ThanicsRobotics/ProjectHaloCAD/ECAD-Files/EAGLE-Files/ThanicsHalo/Drone V3/TOF Sensor Board/TOFSensorBoard.brd

## EAGLE design ECAD-Files/EAGLE-Files/ThanicsHalo/Drone V3/TOF Sensor Board/TOFSensorBoard.brd (2018-07-10)

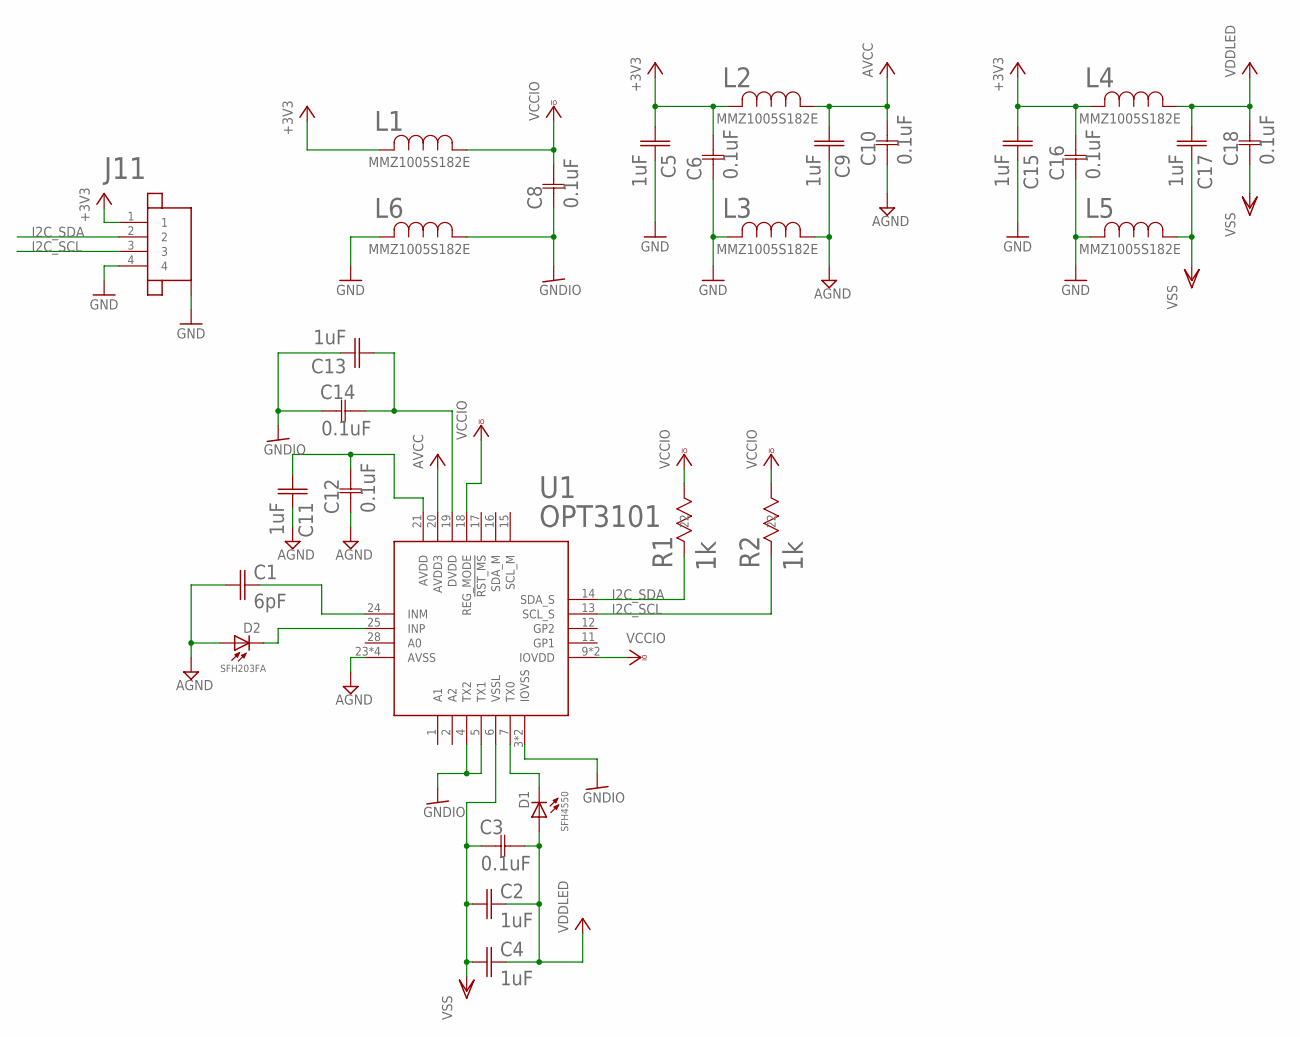
[picture p37: schematic TOFSensorBoard.sch]

Parts:
C1: 6pF; 0402_CAPACITOR
C2, C4, C5, C9, C11, C13, C15, C17: 1uF; 0603_CAPACITOR
C3, C6, C8, C10, C12, C14, C16, C18: 0.1uF; 0402-M
D1: SFH4550; 5MM_LED
D2: SFH203FA; 5MM_LED
J11: JST_SH_4POS
L1, L2, L3, L4, L5, L6: MMZ1005S182ET000IND_1005-M; IND_1005-M
R1, R2: 1k; RC0603N-M
U1: OPT3101; 28-VQFN

Connections:
+3V1: C13.1, C14.2, U1.19 (DVDD)
+3V3: C5.1, C6.2, C15.1, C16.2, J11.1, L1.2, L2.2, L4.2
AGND: C1.1, C9.2, C10.1, C11.2, C12.1, D2.A, L3.1, U1.23 (AVSS), U1.26 (AVSS), U1.27 (AVSS), U1.29 (AVSS)
AVCC: C9.1, C10.2, L2.1, U1.20 (AVDD3)
GND: C5.2, C6.1, C15.2, C16.1, J11.4, J11.P$5 (5), J11.P$6 (5), L3.2, L5.2, L6.2
GNDIO: C8.1, C13.2, C14.1, L6.1, U1.3 (IOVSS), U1.4 (TX2), U1.5 (TX1), U1.8 (IOVSS)
I2C_SCL: J11.3, R2.2 (22), U1.13 (SCL_S)
I2C_SDA: J11.2, R1.2 (22), U1.14 (SDA_S)
unnamed: C11.1, C12.2, U1.21 (AVDD)
unnamed: D1.C, U1.7 (TX0)
unnamed: C1.2, U1.24 (INM)
unnamed: D2.C, U1.25 (INP)
VCCIO: C8.2, L1.1, R1.1 (11), R2.1 (11), U1.9 (IOVDD), U1.10 (IOVDD), U1.18 (REG_MODE)
VDDLED: C2.2, C3.2, C4.2, C17.1, C18.2, D1.A, L4.1
VSS: C2.1, C3.1, C4.1, C17.2, C18.1, L5.1, U1.6 (VSSL)

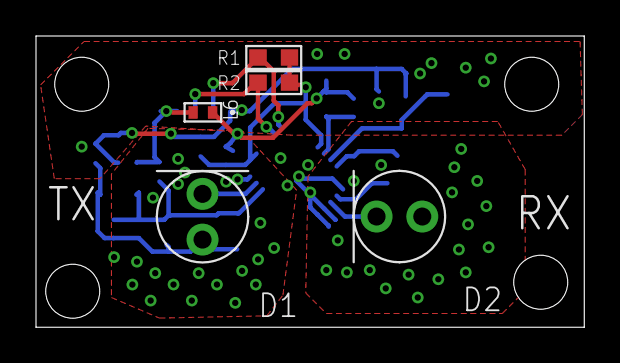
[picture p38: board TOFSensorBoard.brd from above]

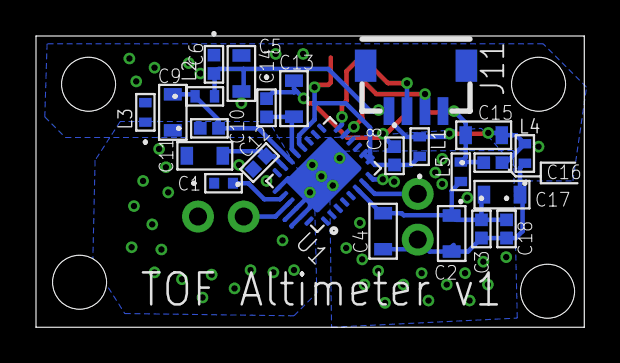
[picture p39: board TOFSensorBoard.brd from below]

Board: 4 copper layers, 30.5 x 16.2 mm, 29 parts (24 on the bottom side), 15 nets.
