ThanicsRobotics/ProjectHaloCAD/ECAD-Files/EAGLE-Files/ThanicsHalo/Drone V1/Gimbal Controller Board/Gimbal Controller Board.brd

## EAGLE design ECAD-Files/EAGLE-Files/ThanicsHalo/Drone V1/Gimbal Controller Board/Gimbal Controller Board.brd (2018-02-16, an earlier design)

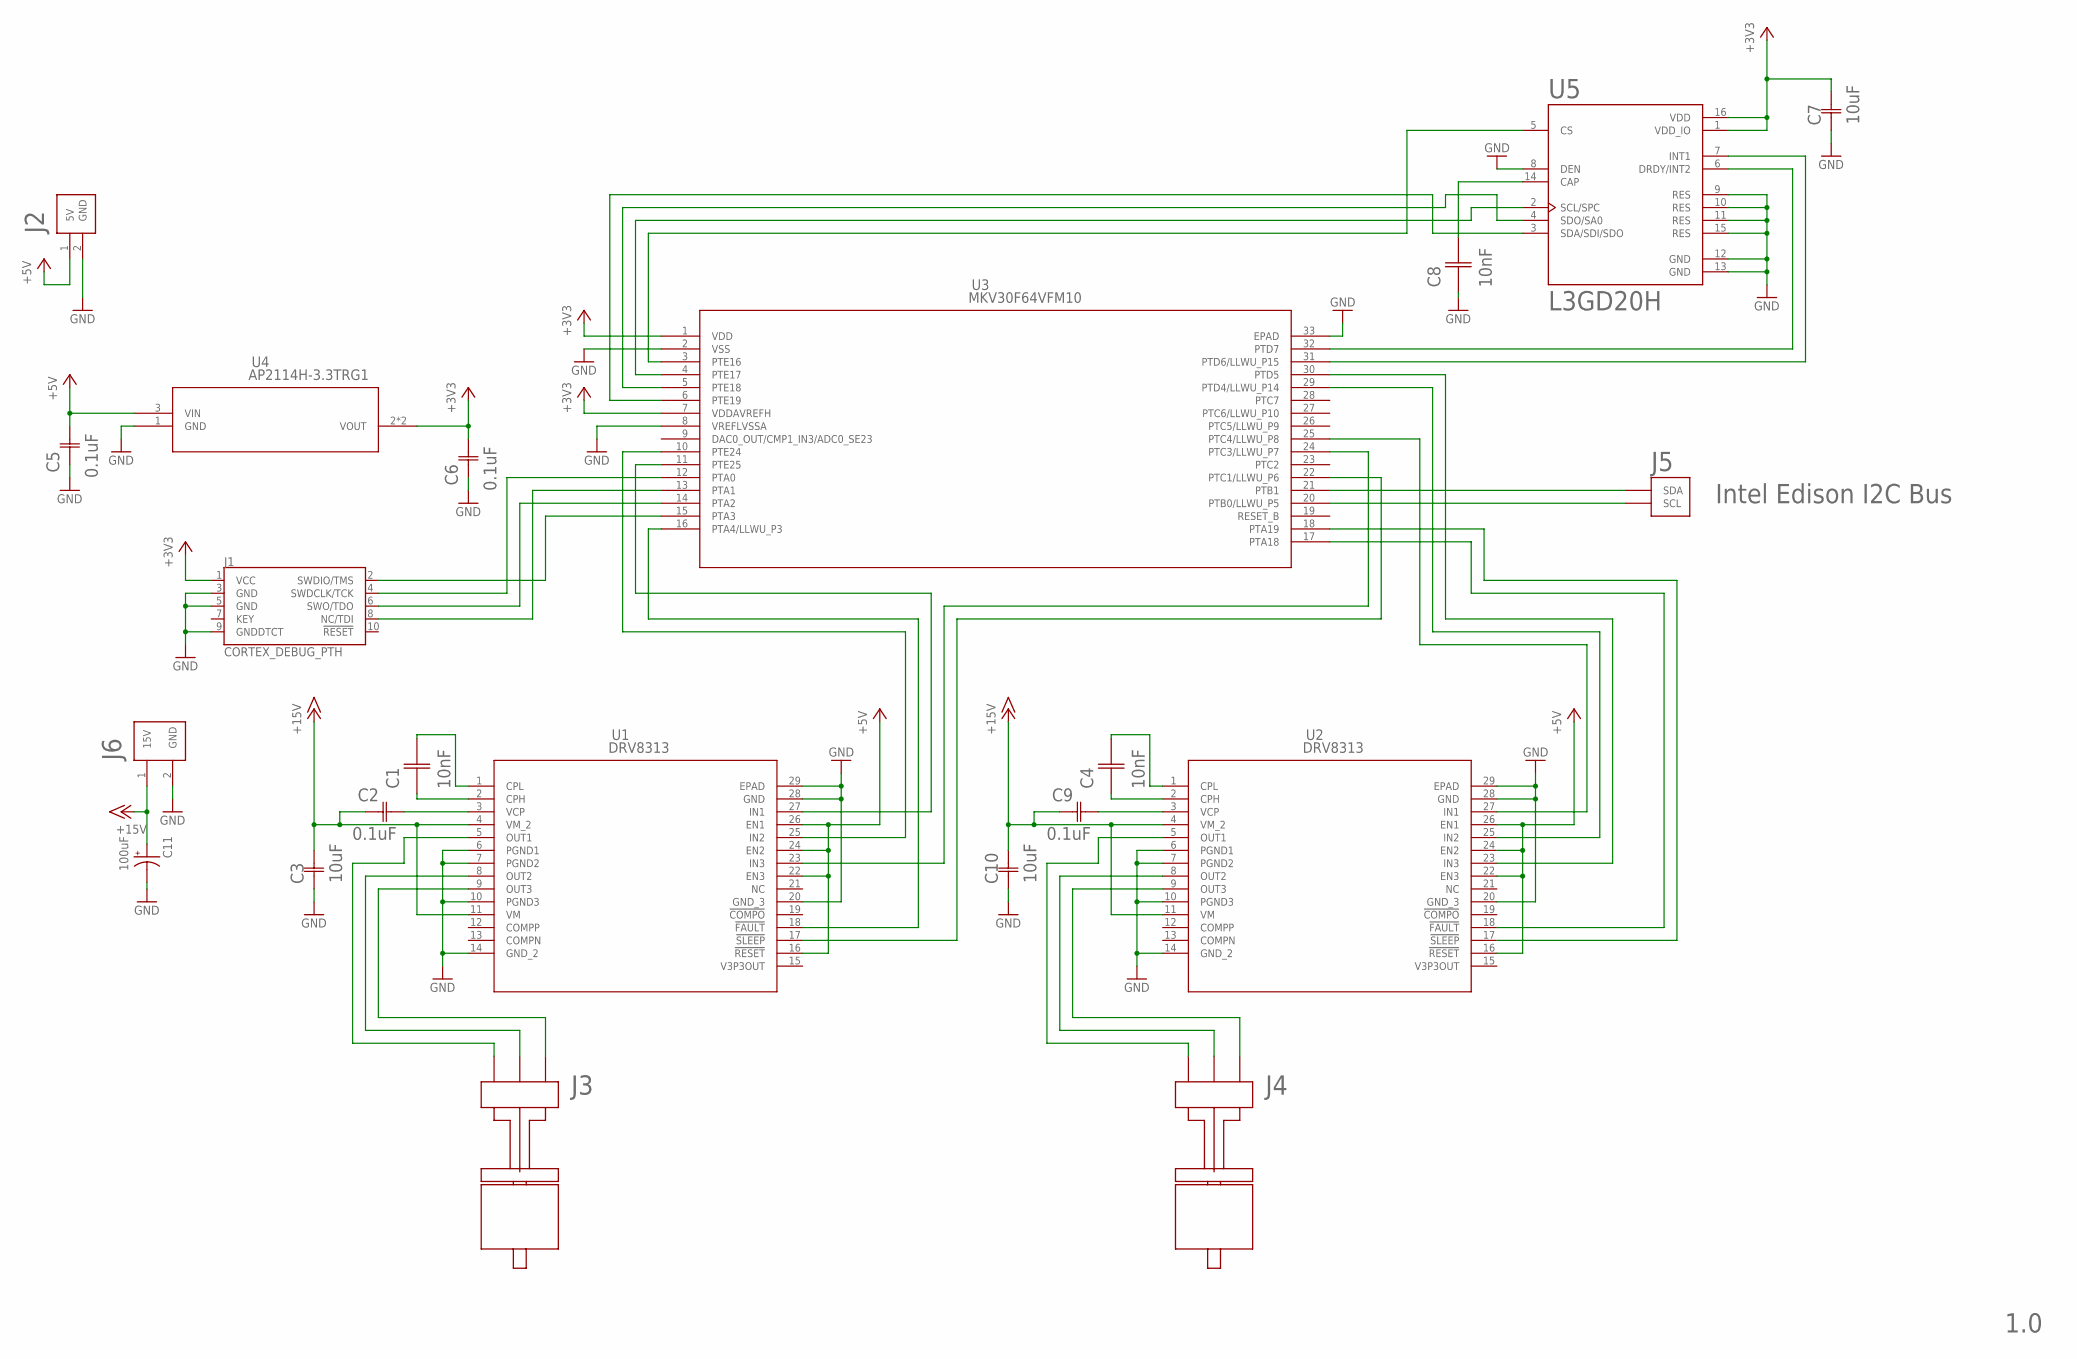
[picture p40: schematic Gimbal Controller Board.sch]

Parts:
C1, C4, C8: 10nF; 0603_CAPACITOR
C2, C5, C6, C9: 0.1uF; 0805
C3, C7, C10: 10uF; G-21
C11: 100uF; 0810_POLCAP
J1: CORTEX_DEBUG_PTH; 2X5-PTH-1.27MM
J2: POWER_CONNECTOR; XH_CONNECTOR
J3, J4: BLDC_MOTOR_CONNECTOR; JST-XH_3POS
J5: I2C_CONNECTOR; XH_CONNECTOR
J6: GIMBAL_POWER_CONNECTOR; XH_CONNECTOR
U1, U2: DRV8313; PWP28_5P18X3P1-M
U3: MKV30F64VFM10; QFN-32_5X5X0.9
U4: AP2114H-3.3TRG1; SOT-223
U5: L3GD20H; LGA16R50P7X5_300X300X100

Connections:
+3V3: C6.2, C7.2 (22), J1.1 (VCC), U3.1 (VDD), U3.7 (VDDAVREFH), U4.2 (VOUT), U4.4 (VOUT), U5.1 (VDD_IO), U5.16 (VDD)
+5V: C5.2, J2.1 (5V), U1.16 (!RESET), U1.22 (EN3), U1.24 (EN2), U1.26 (EN1), U2.16 (!RESET), U2.22 (EN3), U2.24 (EN2), U2.26 (EN1), U4.3 (VIN)
+15V: C2.1, C3.2 (22), C9.1, C10.2 (22), C11.+, J6.1 (15V), U1.4 (VM_2), U1.11 (VM), U2.4 (VM_2), U2.11 (VM)
GND: C3.1 (11), C5.1, C6.1, C7.1 (11), C8.1, C10.1 (11), C11.-, J1.3 (GND), J1.5 (GND), J1.9 (GNDDTCT), J2.2 (GND), J6.2 (GND), U1.6 (PGND1), U1.7 (PGND2), U1.10 (PGND3), U1.14 (GND_2), U1.20 (GND_3), U1.28 (GND), U1.29 (EPAD), U2.6 (PGND1), U2.7 (PGND2), U2.10 (PGND3), U2.14 (GND_2), U2.20 (GND_3), U2.28 (GND), U2.29 (EPAD), U3.2 (VSS), U3.8 (VREFLVSSA), U3.33 (EPAD), U4.1 (GND), U5.8 (DEN), U5.9 (RES), U5.10 (RES), U5.11 (RES), U5.12 (GND), U5.13 (GND), U5.15 (RES)
unnamed: C1.1, U1.2 (CPH)
unnamed: C1.2, U1.1 (CPL)
unnamed: U1.25 (IN2), U3.10 (PTE24)
unnamed: U1.17 (!SLEEP), U3.22 (PTC1/LLWU_P6)
unnamed: J3.P$1 (1), U1.5 (OUT1)
unnamed: U1.23 (IN3), U3.24 (PTC3/LLWU_P7)
unnamed: U1.18 (!FAULT), U3.16 (PTA4/LLWU_P3)
unnamed: U1.27 (IN1), U3.11 (PTE25)
unnamed: J1.4 (SWDCLK/TCK), U3.12 (PTA0)
unnamed: J1.6 (SWO/TDO), U3.14 (PTA2)
unnamed: J1.8 (NC/TDI), U3.13 (PTA1)
unnamed: J1.2 (SWDIO/TMS), U3.15 (PTA3)
unnamed: J3.P$2 (2), U1.8 (OUT2)
unnamed: J3.P$3 (3), U1.9 (OUT3)
unnamed: J5.1 (SCL), U3.20 (PTB0/LLWU_P5)
unnamed: J5.2 (SDA), U3.21 (PTB1)
unnamed: U3.3 (PTE16), U5.5 (CS)
unnamed: U3.4 (PTE17), U5.2 (SCL/SPC)
unnamed: U3.5 (PTE18), U5.4 (SDO/SA0)
unnamed: U3.6 (PTE19), U5.3 (SDA/SDI/SDO)
unnamed: C8.2, U5.14 (CAP)
unnamed: C2.2, U1.3 (VCP)
unnamed: C4.1, U2.2 (CPH)
unnamed: C4.2, U2.1 (CPL)
unnamed: U3.32 (PTD7), U5.6 (DRDY/INT2)
unnamed: U3.31 (PTD6/LLWU_P15), U5.7 (INT1)
unnamed: U2.25 (IN2), U3.29 (PTD4/LLWU_P14)
unnamed: U2.27 (IN1), U3.25 (PTC4/LLWU_P8)
unnamed: U2.23 (IN3), U3.30 (PTD5)
unnamed: U2.18 (!FAULT), U3.17 (PTA18)
unnamed: U2.17 (!SLEEP), U3.18 (PTA19)
unnamed: J4.P$1 (1), U2.5 (OUT1)
unnamed: J4.P$2 (2), U2.8 (OUT2)
unnamed: J4.P$3 (3), U2.9 (OUT3)
unnamed: C9.2, U2.3 (VCP)

Notes on the sheet:
Intel Edison I2C Bus
1.0

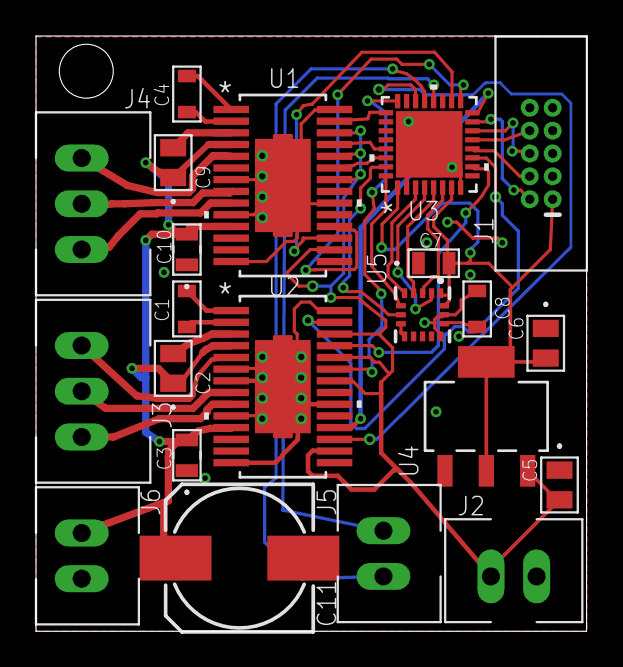
[picture p41: board ECAD-Files/EAGLE-Files/ThanicsHalo/Drone V1/Gimbal Controller Board/G… from above]

Board: 2 copper layers, 30.6 x 33.1 mm, 22 parts (0 on the bottom side), 39 nets.
