ThanicsRobotics/ProjectHaloCAD/ECAD-Files/EAGLE-Files/ThanicsHalo/Drone V2/Sensor Board B/Sensor Board B.brd

## EAGLE design ECAD-Files/EAGLE-Files/ThanicsHalo/Drone V2/Sensor Board B/Sensor Board B.brd (2018-02-16, an earlier design)

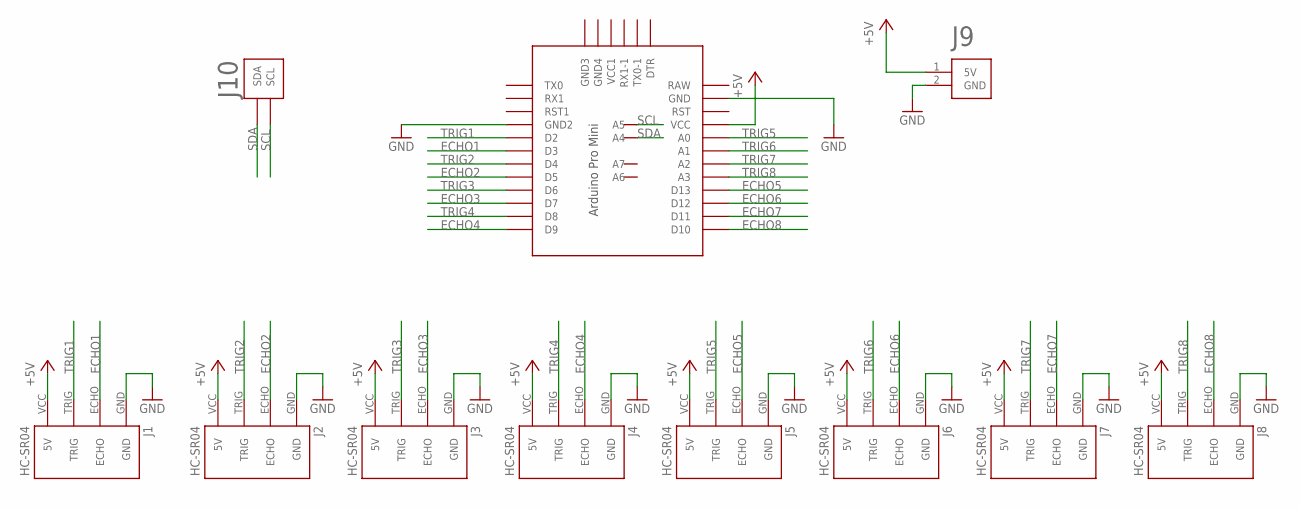
[picture p42: schematic Sensor Board B.sch]

Parts:
J1, J2, J3, J4, J5, J6, J7, J8: HC-SR04; HC-SR04_FOOTPRINT
J9: POWER_CONNECTOR; XH_CONNECTOR
J10: I2C_CONNECTOR; XH_CONNECTOR
U1: PRO-MINI-2

Connections:
+5V: J1.VCC (5V), J2.VCC (5V), J3.VCC (5V), J4.VCC (5V), J5.VCC (5V), J6.VCC (5V), J7.VCC (5V), J8.VCC (5V), J9.1 (5V), U1.VCC
ECHO1: J1.ECHO, U1.D3
ECHO2: J2.ECHO, U1.D5
ECHO3: J3.ECHO, U1.D7
ECHO4: J4.ECHO, U1.D9
ECHO5: J5.ECHO, U1.D13
ECHO6: J6.ECHO, U1.D12
ECHO7: J7.ECHO, U1.D11
ECHO8: J8.ECHO, U1.D10
GND: J1.GND, J2.GND, J3.GND, J4.GND, J5.GND, J6.GND, J7.GND, J8.GND, J9.2 (GND), U1.GND, U1.GND1 (GND2)
SCL: J10.1 (SCL), U1.A5
SDA: J10.2 (SDA), U1.A4
TRIG1: J1.TRIG, U1.D2
TRIG2: J2.TRIG, U1.D4
TRIG3: J3.TRIG, U1.D6
TRIG4: J4.TRIG, U1.D8
TRIG5: J5.TRIG, U1.A0
TRIG6: J6.TRIG, U1.A1
TRIG7: J7.TRIG, U1.A2
TRIG8: J8.TRIG, U1.A3

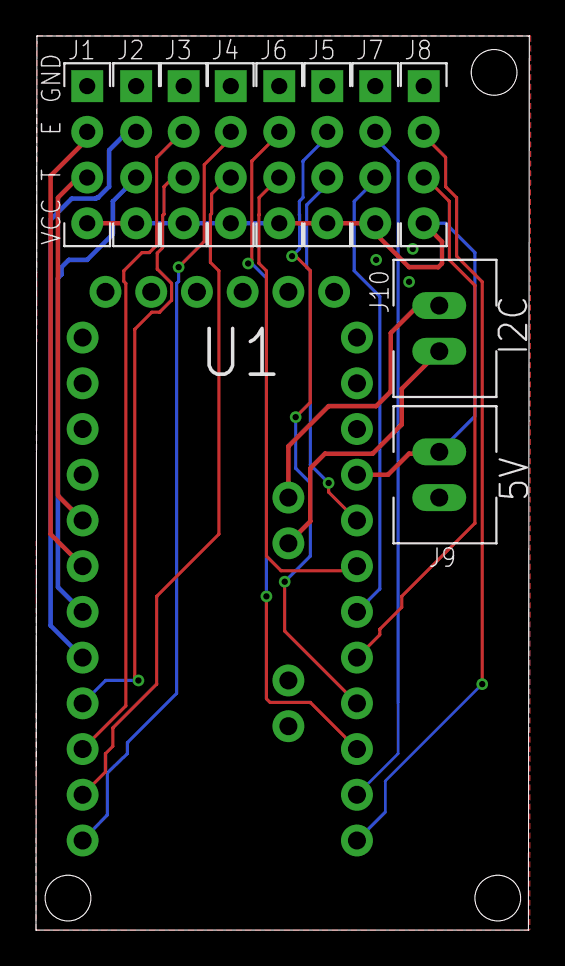
[picture p43: board Sensor Board B.brd from above]

Board: 2 copper layers, 27.4 x 49.7 mm, 11 parts (0 on the bottom side), 20 nets.
