ThanicsRobotics/ProjectHaloCAD/ECAD-Files/EAGLE-Files/ThanicsHalo/Drone V2/Drone-Battery Connection/Drone-Battery Connection.brd

## EAGLE design ECAD-Files/EAGLE-Files/ThanicsHalo/Drone V2/Drone-Battery Connection/Drone-Battery Connection.brd (2018-02-16, an earlier design)

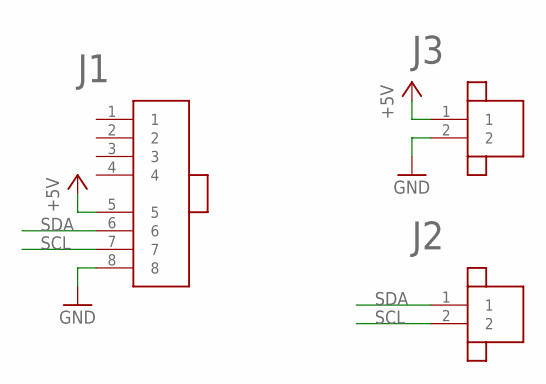
[picture p44: schematic Drone-Battery Connection.sch]

Parts:
J1: SPRING_BTB_8POS_MALE
J2, J3: JST_SH_2POS

Connections:
+5V: J1.5, J3.1
GND: J1.8, J3.2
SCL: J1.7, J2.2
SDA: J1.6, J2.1

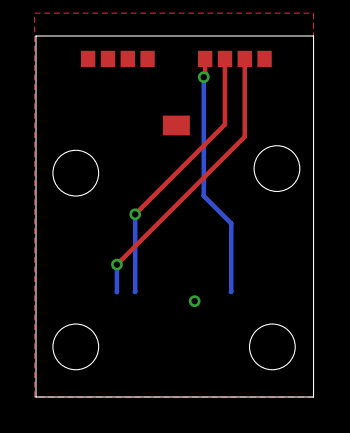
[picture p45: board Drone-Battery Connection.brd from above]

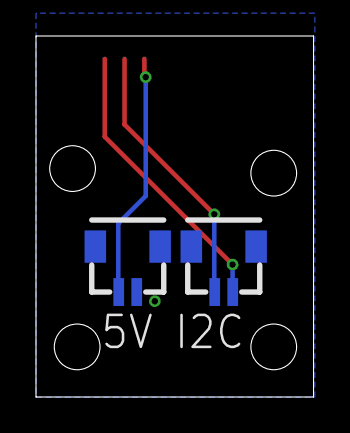
[picture p46: board Drone-Battery Connection.brd from below]

Board: 2 copper layers, 15.4 x 20.1 mm, 3 parts (2 on the bottom side), 4 nets.
