ThanicsRobotics/ProjectHaloCAD/ECAD-Files/EAGLE-Files/ThanicsHalo/Drone V1/Relay Board A/Relay Board A.brd

## EAGLE design ECAD-Files/EAGLE-Files/ThanicsHalo/Drone V1/Relay Board A/Relay Board A.brd (2018-02-16, an earlier design)

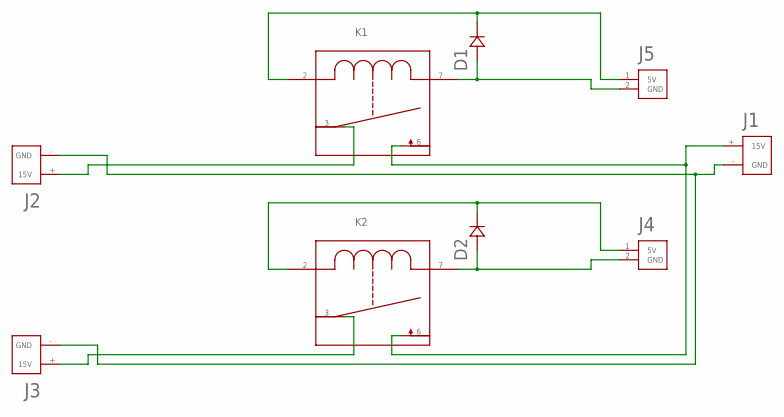
[picture p47: schematic Relay Board A.sch]

Parts:
D1, D2: 1N4148W-7-FSOD123-M; SOD123-M
J1, J2, J3: ESC_CONTACTS; XT60_CONNECTOR
J4, J5: POWER_CONNECTOR; XH_CONNECTOR
K1, K2: T9AS1D12-24; RELAY_T9AS

Connections:
GND: J1.- (GND), J2.- (GND), J3.- (GND)
unnamed: J1.+ (15V), K1.6 (3), K2.6 (3)
unnamed: J2.+ (15V), K1.3 (2)
unnamed: J3.+ (15V), K2.3 (2)
unnamed: D1.C (12), J5.1 (5V), K1.2 (1)
unnamed: D1.A (21), J5.2 (GND), K1.7 (4)
unnamed: D2.C (12), J4.1 (5V), K2.2 (1)
unnamed: D2.A (21), J4.2 (GND), K2.7 (4)

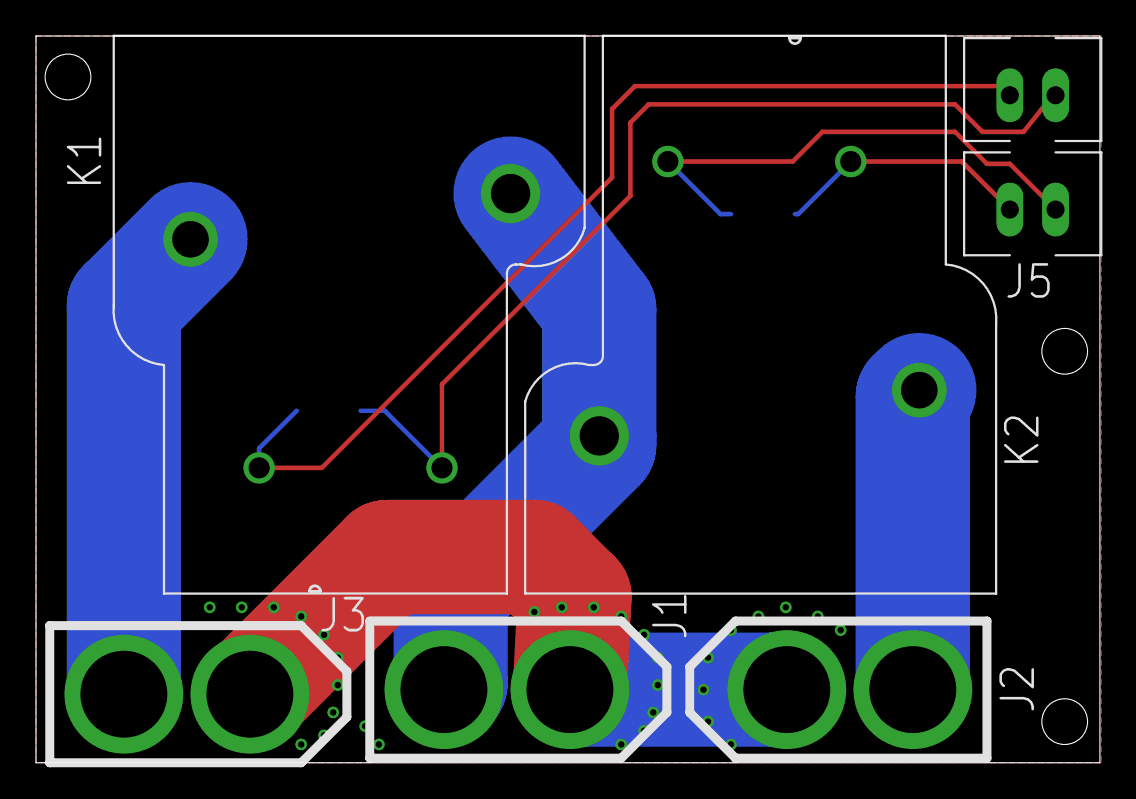
[picture p48: board Relay Board A.brd from above]

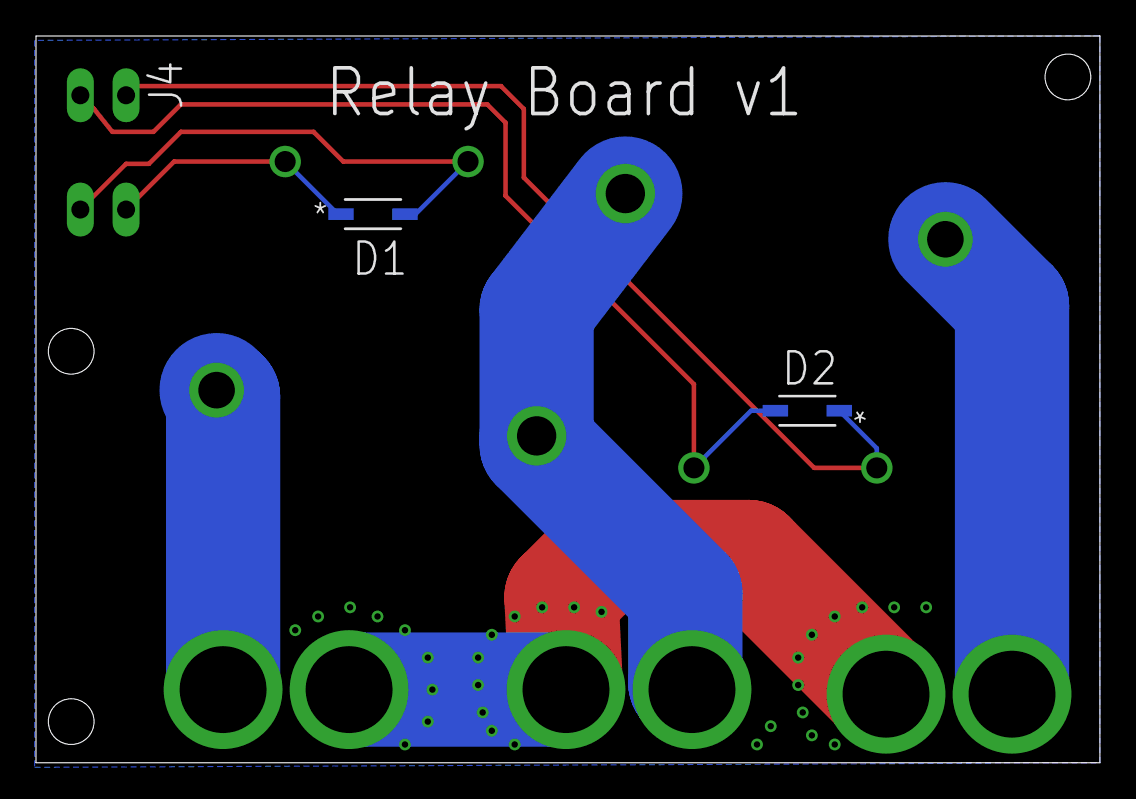
[picture p49: board Relay Board A.brd from below]

Board: 2 copper layers, 59.1 x 40.4 mm, 9 parts (2 on the bottom side), 8 nets.
