ThanicsRobotics/ProjectHaloCAD/ECAD-Files/EAGLE-Files/ThanicsHalo/Drone V1/Central Board/Central Board.brd

## EAGLE design ECAD-Files/EAGLE-Files/ThanicsHalo/Drone V1/Central Board/Central Board.brd (2018-02-16, an earlier design)

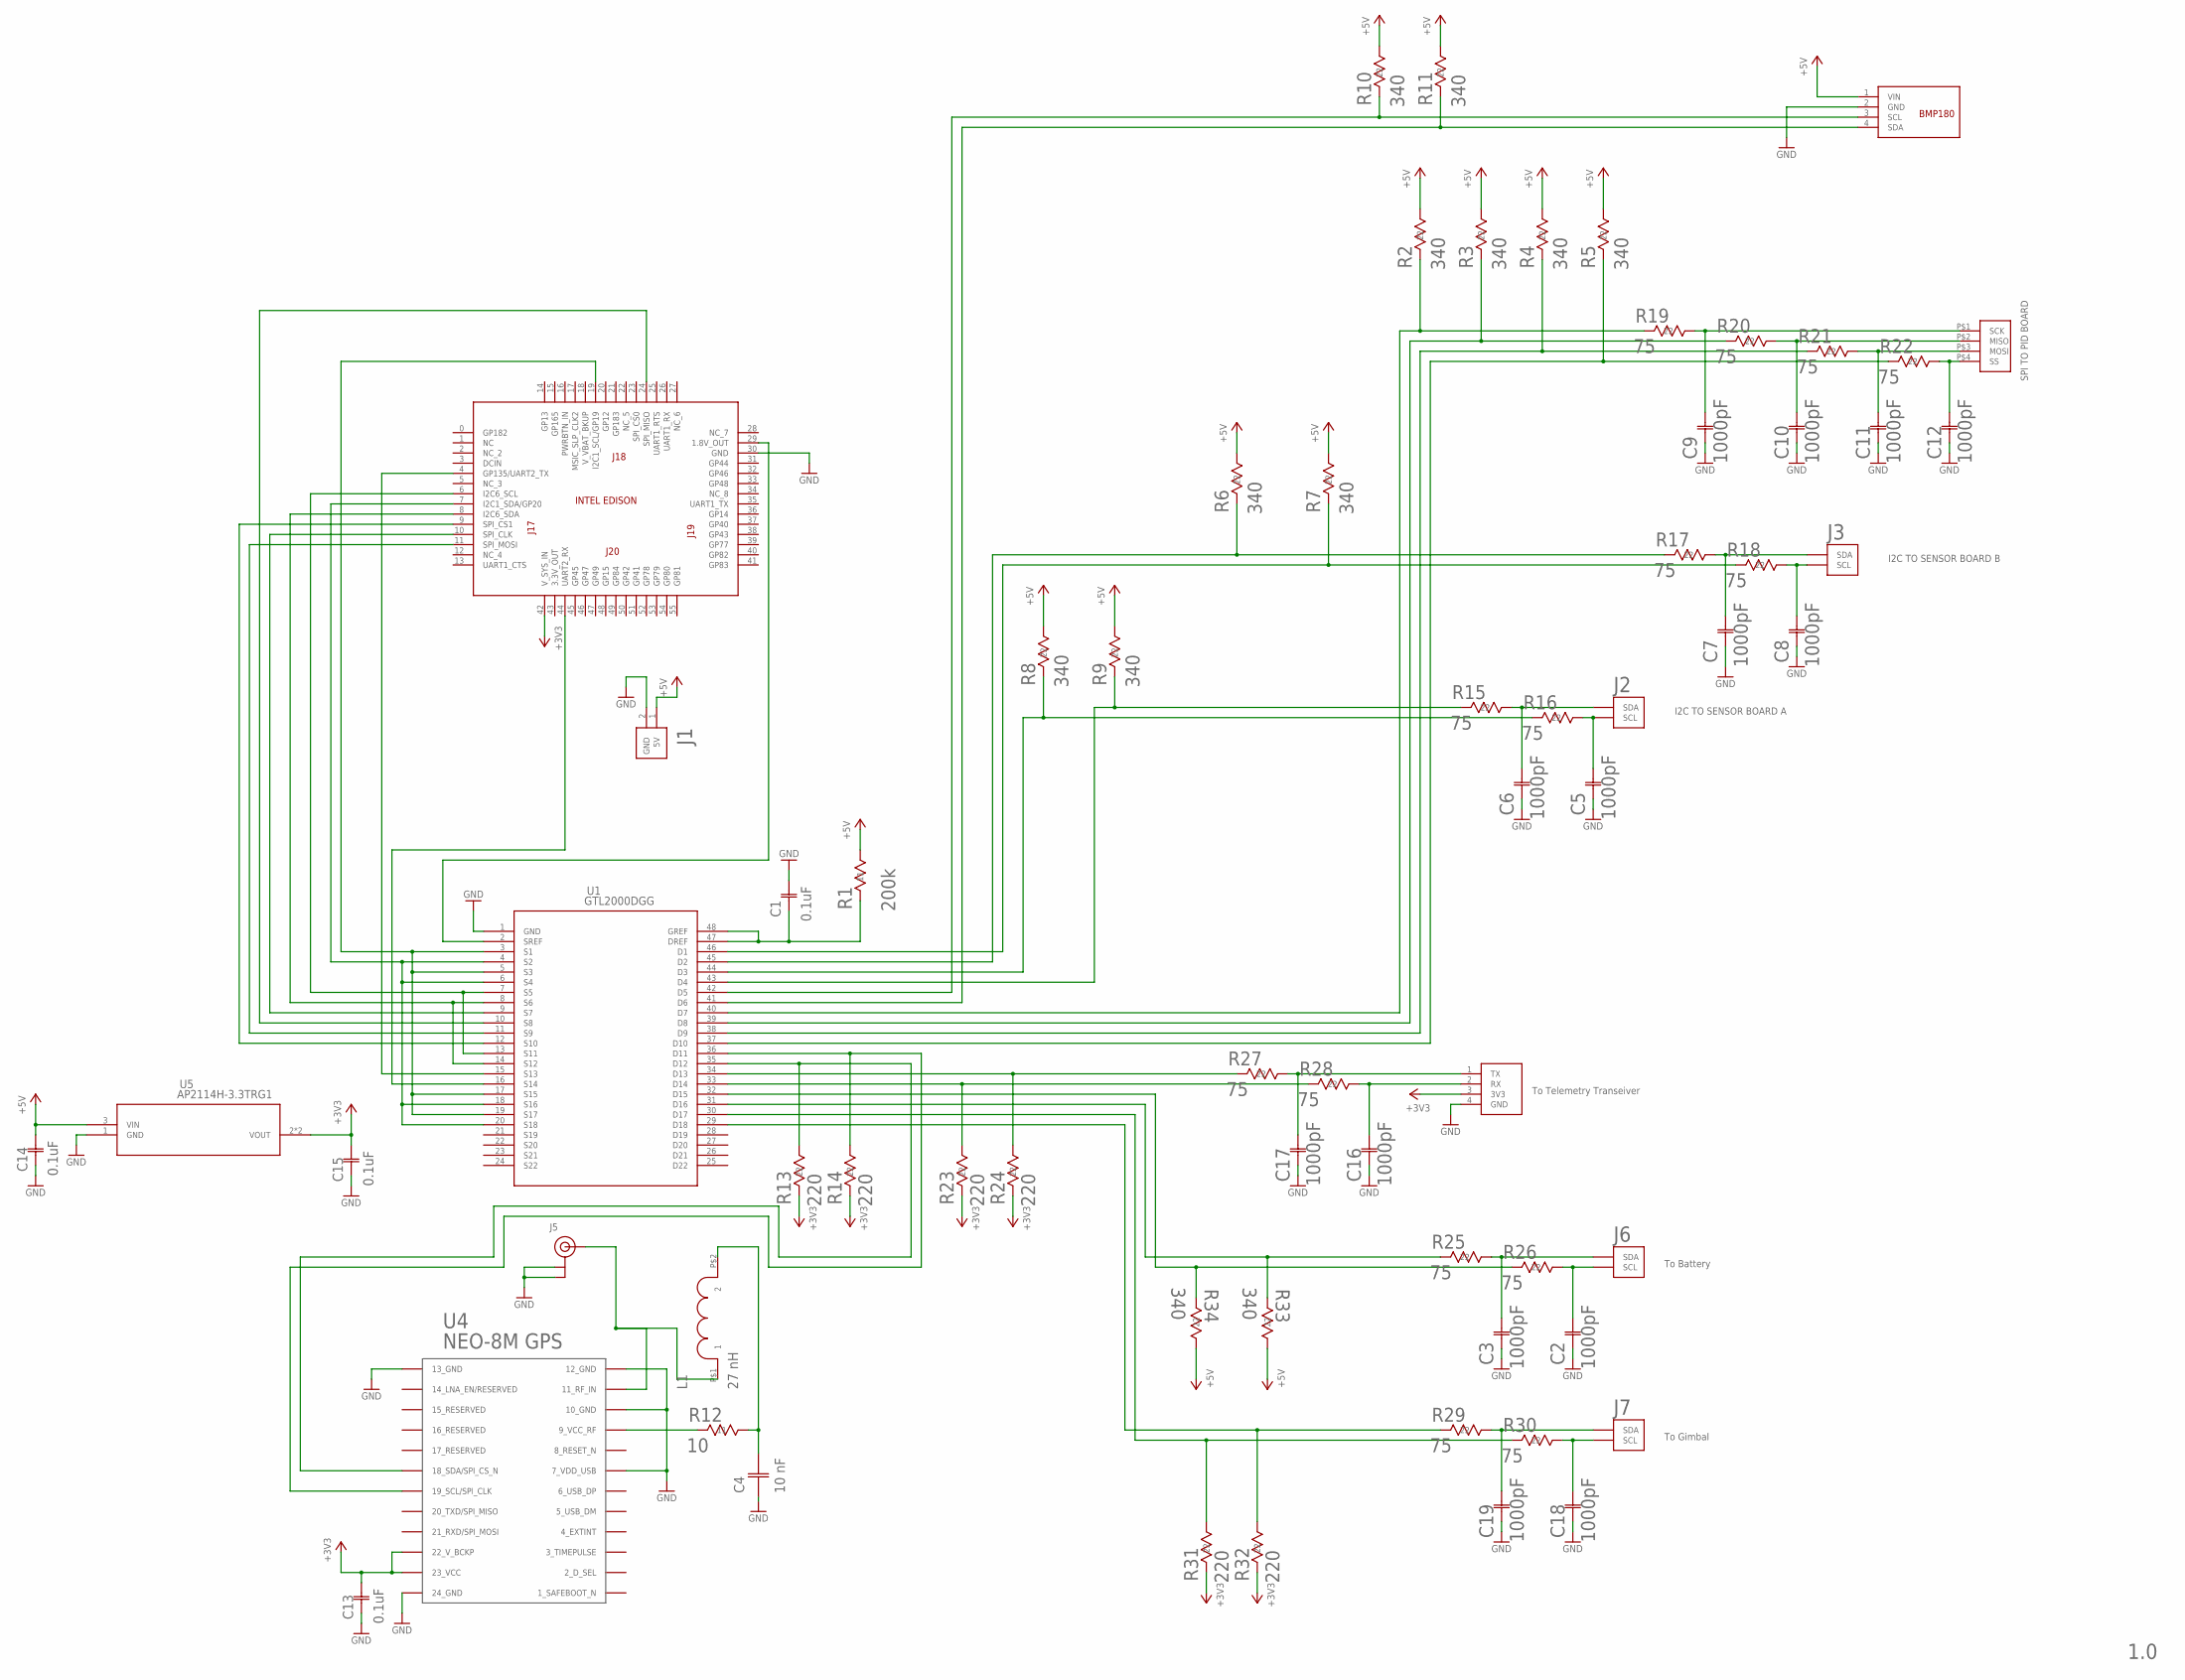
[picture p50: schematic Central Board.sch]

Parts:
C1, C13, C14, C15: 0.1uF; 0805
C2, C3, C5, C6, C7, C8, C9, C10, C11, C12, C16, C17, C18, C19: 1000pF; G-155-M
C4: 10 nF; 0603_CAPACITOR
J1: POWER_CONNECTOR; XH_CONNECTOR
J2, J3, J6, J7: I2C_CONNECTOR; XH_CONNECTOR
J4: SPI_CONNECTOR; JST-XH_4POS
J5: U.FL
L1: 27 nH; 0402_INDUCTOR
R1: 200k; STA_RMCF0603
R2, R3, R4, R5, R6, R7, R8, R9, R10, R11, R33, R34: 340; RC0603N
R12: 10; STA_RNCP0805-M
R13, R14, R23, R24, R31, R32: 220; RC0603N-M
R15, R16, R17, R18, R19, R20, R21, R22, R25, R26, R27, R28, R29, R30: 75; RC0402N-M
U1: GTL2000DGG; SOT362-1
U3: INTEL_EDISON
U4: NEO-M8
U5: AP2114H-3.3TRG1; SOT-223
U9: BMP180_BARO
U$1: 4_PIN_TELE_CONNECTOR

Connections:
3.3V_OUT: U3.43 (3.3V_OUT)
+3V3: C13.2, C15.2, R13.2 (22), R14.2 (22), R23.2 (22), R24.2 (22), R31.2 (22), R32.2 (22), U3.42 (V_SYS_IN), U4.22 (22_V_BCKP), U4.23 (23_VCC), U5.2 (VOUT), U5.4 (VOUT), U$1.3 (3V3)
+5V: C14.2, J1.1 (5V), R1.2 (22), R2.1 (11), R3.1 (11), R4.1 (11), R5.1 (11), R6.1 (11), R7.1 (11), R8.1 (11), R9.1 (11), R10.1 (11), R11.1 (11), R33.1 (11), R34.1 (11), U5.3 (VIN), U9.1 (VIN)
DCIN: U3.3 (DCIN)
GND: C1.2, C2.1 (11), C3.1 (11), C4.1, C5.1 (11), C6.1 (11), C7.1 (11), C8.1 (11), C9.1 (11), C10.1 (11), C11.1 (11), C12.1 (11), C13.1, C14.1, C15.1, C16.1 (11), C17.1 (11), C18.1 (11), C19.1 (11), J1.2 (GND), J5.P$1 (GND), J5.P$2 (GND), U1.1 (GND), U3.30 (GND), U4.7 (7_VDD_USB), U4.10 (10_GND), U4.12 (12_GND), U4.13 (13_GND), U4.24 (24_GND), U5.1 (GND), U9.2 (GND), U$1.4 (GND)
MSIC_SLP_CLK2: U3.17 (MSIC_SLP_CLK2)
unnamed: J5.P$3 (SIGNAL), L1.P$1 (1), U4.11 (11_RF_IN)
unnamed: U1.3 (S1), U1.5 (S3), U1.17 (S15), U1.19 (S17), U3.19 (I2C1_SCL/GP19)
unnamed: U1.4 (S2), U1.6 (S4), U1.18 (S16), U1.20 (S18), U3.7 (I2C1_SDA/GP20)
unnamed: R7.2 (22), R18.2 (22), U1.46 (D1)
unnamed: R6.2 (22), R17.2 (22), U1.45 (D2)
unnamed: C18.2 (22), J7.1 (SCL), R30.1 (11)
unnamed: R9.2 (22), R15.2 (22), U1.43 (D4)
unnamed: U1.7 (S5), U1.13 (S11), U3.6 (I2C6_SCL)
unnamed: U1.8 (S6), U1.14 (S12), U3.8 (I2C6_SDA)
unnamed: R10.2 (22), U1.42 (D5), U9.3 (SCL)
unnamed: U1.2 (SREF), U3.29 (1.8V_OUT)
unnamed: R14.1 (11), U1.36 (D11), U4.19 (19_SCL/SPI_CLK)
unnamed: R12.1 (11), U4.9 (9_VCC_RF)
unnamed: R11.2 (22), U1.41 (D6), U9.4 (SDA)
unnamed: U1.9 (S7), U3.10 (SPI_CLK)
unnamed: C19.2 (22), J7.2 (SDA), R29.1 (11)
unnamed: U1.10 (S8), U3.24 (SPI_MISO)
unnamed: U1.16 (S14), U3.44 (UART2_RX)
unnamed: U1.11 (S9), U3.11 (SPI_MOSI)
unnamed: U1.15 (S13), U3.4 (GP135/UART2_TX)
unnamed: U1.12 (S10), U3.9 (SPI_CS1)
unnamed: R23.1 (11), R28.2 (22), U1.33 (D14)
unnamed: C1.1, R1.1 (11), U1.47 (DREF), U1.48 (GREF)
unnamed: R24.1 (11), R27.2 (22), U1.34 (D13)
unnamed: C4.2, L1.P$2 (2), R12.2 (22)
unnamed: R13.1 (11), U1.35 (D12), U4.18 (18_SDA/SPI_CS_N)
unnamed: C5.2 (22), J2.1 (SCL), R16.1 (11)
unnamed: R8.2 (22), R16.2 (22), U1.44 (D3)
unnamed: C6.2 (22), J2.2 (SDA), R15.1 (11)
unnamed: C8.2 (22), J3.1 (SCL), R18.1 (11)
unnamed: C7.2 (22), J3.2 (SDA), R17.1 (11)
unnamed: R30.2 (22), R31.1 (11), U1.30 (D17)
unnamed: C12.2 (22), J4.P$4 (SS), R22.1 (11)
unnamed: C11.2 (22), J4.P$3 (MOSI), R21.1 (11)
unnamed: C9.2 (22), J4.P$1 (SCK), R19.1 (11)
unnamed: C10.2 (22), J4.P$2 (MISO), R20.1 (11)
unnamed: C2.2 (22), J6.1 (SCL), R26.1 (11)
unnamed: R29.2 (22), R32.1 (11), U1.29 (D18)
unnamed: C3.2 (22), J6.2 (SDA), R25.1 (11)
unnamed: C16.2 (22), R28.1 (11), U$1.2 (RX)
unnamed: R25.2 (22), R33.2 (22), U1.31 (D16)
unnamed: C17.2 (22), R27.1 (11), U$1.1 (TX)
unnamed: R26.2 (22), R34.2 (22), U1.32 (D15)
unnamed: R5.2 (22), R22.2 (22), U1.37 (D10)
unnamed: R4.2 (22), R21.2 (22), U1.38 (D9)
unnamed: R3.2 (22), R20.2 (22), U1.39 (D8)
unnamed: R2.2 (22), R19.2 (22), U1.40 (D7)
PWRBTN_IN: U3.16 (PWRBTN_IN)
V_VBAT_BKUP: U3.18 (V_VBAT_BKUP)

Notes on the sheet:
I2C TO SENSOR BOARD A
I2C TO SENSOR BOARD B
SPI TO PID BOARD
To Telemetry Transeiver
To Battery
To Gimbal
1.0

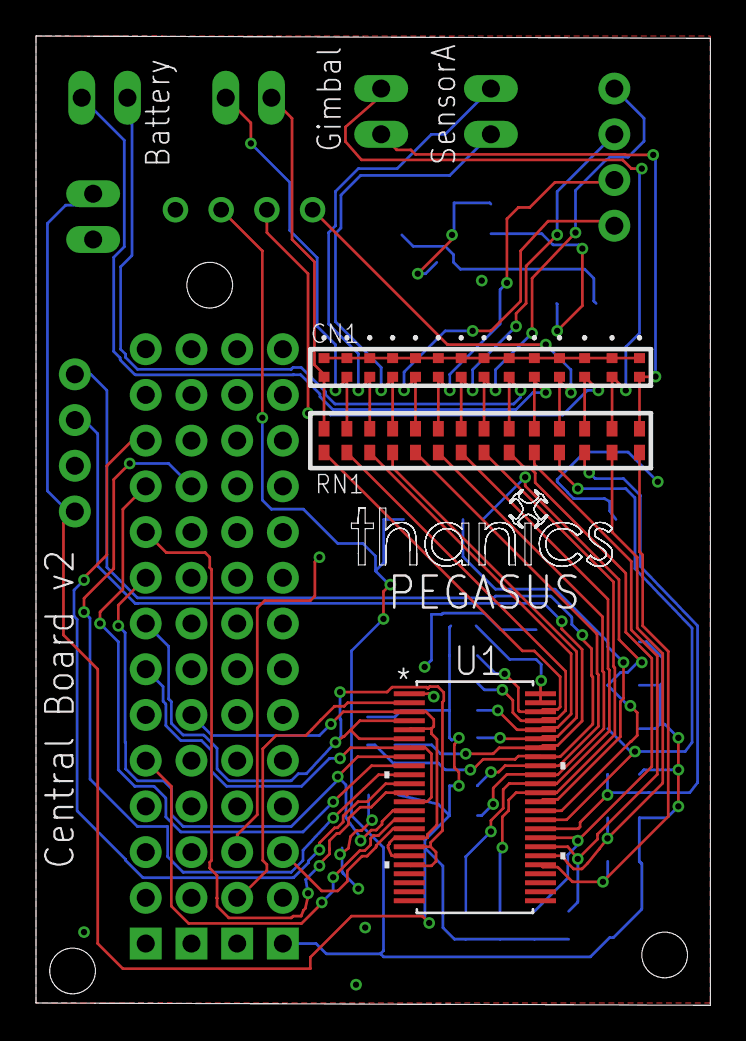
[picture p51: board Central Board.brd from above]

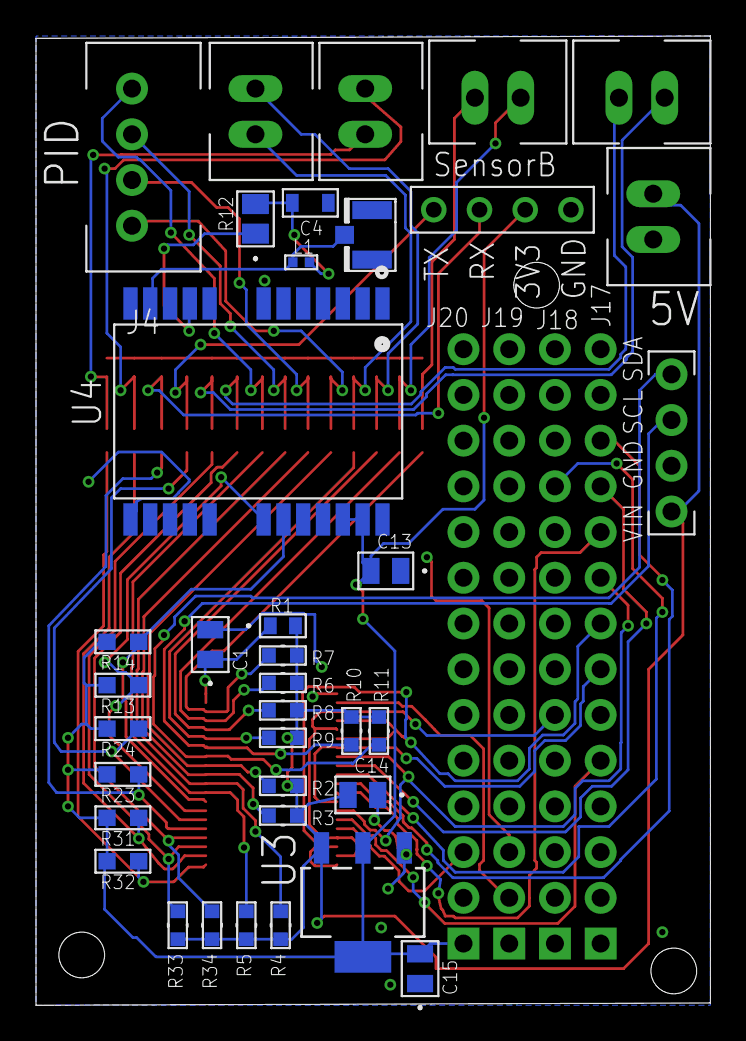
[picture p52: board Central Board.brd from below]

Board: 2 copper layers, 37.5 x 53.8 mm, 67 parts (37 on the bottom side), 50 nets.
