ThanicsRobotics/ProjectHaloCAD/ECAD-Files/EAGLE-Files/ThanicsHalo/Drone V2/IMU Board/IMU Board.brd

## EAGLE design ECAD-Files/EAGLE-Files/ThanicsHalo/Drone V2/IMU Board/IMU Board.brd (2018-02-16, an earlier design)

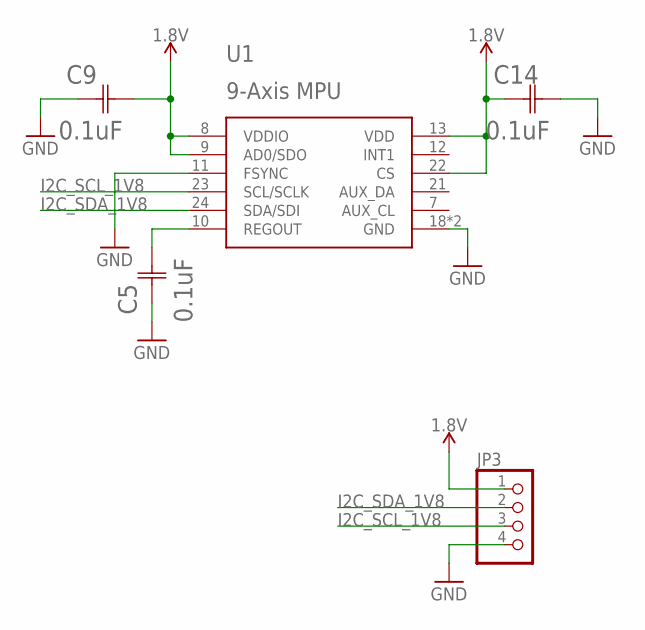
[picture p53: schematic IMU Board.sch]

Parts:
C5, C9, C14: 0.1uF; 0805
JP3: PINHD-1X4; 1X04
U1: ICM-20948; QFN40P300X300X105-25N

Connections:
1.8V: C9.2, C14.1, JP3.1, U1.8 (VDDIO), U1.9 (AD0/SDO), U1.13 (VDD), U1.22 (CS)
GND: C5.1, C9.1, C14.2, JP3.4, U1.11 (FSYNC), U1.18 (GND), U1.20 (GND)
I2C_SCL_1V8: JP3.3, U1.23 (SCL/SCLK)
I2C_SDA_1V8: JP3.2, U1.24 (SDA/SDI)
unnamed: C5.2, U1.10 (REGOUT)

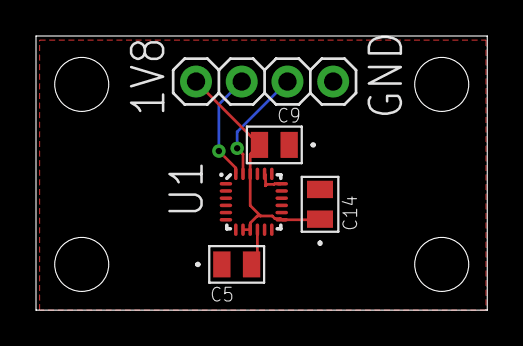
[picture p54: board IMU Board.brd from above]

Board: 2 copper layers, 25.1 x 15.2 mm, 5 parts (0 on the bottom side), 5 nets.
