ThanicsRobotics/ProjectHaloCAD/ECAD-Files/EAGLE-Files/ThanicsHalo/Drone V1/PID Board/PID Board.brd

## EAGLE design ECAD-Files/EAGLE-Files/ThanicsHalo/Drone V1/PID Board/PID Board.brd (2018-02-16, an earlier design)

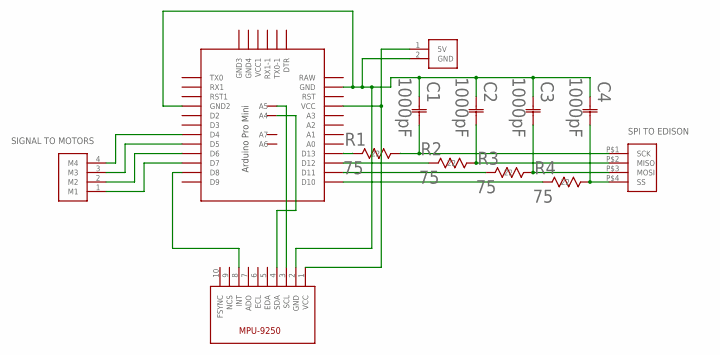
[picture p55: schematic PID Board.sch]

Parts:
C1, C2, C3, C4: 1000pF; G-155-M
J1: POWER_CONNECTOR; XH_CONNECTOR
J2: SPI_CONNECTOR; JST-XH_4POS
J3: 4_PIN_CONNECTOR
R1, R2, R3, R4: 75; RC0402N-M
U1: PRO-MINI-2
U2: MPU-9250

Connections:
GND: C1.1 (11), C2.1 (11), C3.1 (11), C4.1 (11), J1.2 (GND), U1.GND, U1.GND1 (GND2), U2.2 (GND)
unnamed: J1.1 (5V), U1.VCC, U2.1 (VCC)
unnamed: R1.2 (22), U1.D13
unnamed: U1.D8, U2.8 (INT)
unnamed: U1.A4, U2.4 (SDA)
unnamed: U1.A5, U2.3 (SCL)
unnamed: R2.2 (22), U1.D12
unnamed: R3.2 (22), U1.D11
unnamed: R4.2 (22), U1.D10
unnamed: C4.2 (22), J2.P$4 (SS), R4.1 (11)
unnamed: J3.1 (M1), U1.D7
unnamed: J3.2 (M2), U1.D6
unnamed: J3.3 (M3), U1.D5
unnamed: J3.4 (M4), U1.D4
unnamed: C3.2 (22), J2.P$3 (MOSI), R3.1 (11)
unnamed: C2.2 (22), J2.P$2 (MISO), R2.1 (11)
unnamed: C1.2 (22), J2.P$1 (SCK), R1.1 (11)

Notes on the sheet:
SIGNAL TO MOTORS
SPI TO EDISON

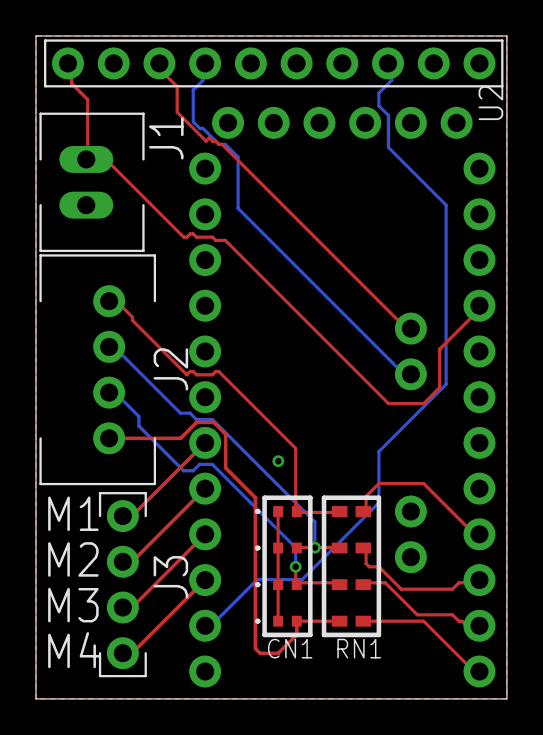
[picture p56: board PID Board.brd from above]

Board: 2 copper layers, 26.2 x 36.8 mm, 13 parts (0 on the bottom side), 17 nets.
