ThanicsRobotics/ProjectHaloCAD/ECAD-Files/EAGLE-Files/ThanicsHalo/Drone V2/Gimbal IMU Board/Gimbal IMU Board.brd

## EAGLE design ECAD-Files/EAGLE-Files/ThanicsHalo/Drone V2/Gimbal IMU Board/Gimbal IMU Board.brd (2018-02-16, an earlier design)

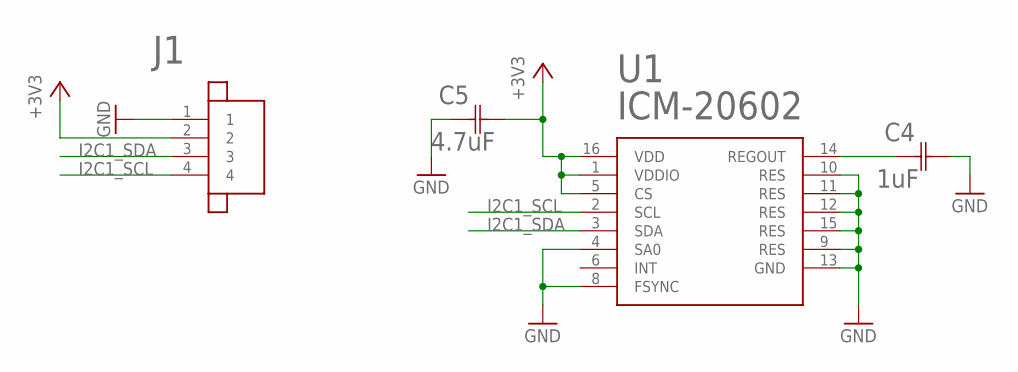
[picture p57: schematic Gimbal IMU Board.sch]

Parts:
C4: 1uF; YAG_CC0805
C5: 4.7uF; 0603-M
J1: JST_SH_4POS
U1: ICM-20602; 16LGA

Connections:
+3V3: C5.2, J1.2, U1.1 (VDDIO), U1.5 (CS), U1.16 (VDD)
GND: C4.2 (22), C5.1, J1.1, U1.4 (SA0), U1.8 (FSYNC), U1.9 (RES), U1.10 (RES), U1.11 (RES), U1.12 (RES), U1.13 (GND), U1.15 (RES)
I2C1_SCL: J1.4, U1.2 (SCL)
I2C1_SDA: J1.3, U1.3 (SDA)
unnamed: C4.1 (11), U1.14 (REGOUT)

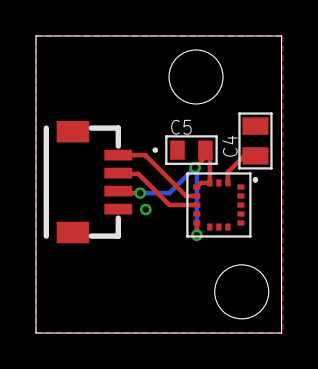
[picture p58: board Gimbal IMU Board.brd from above]

Board: 2 copper layers, 13.6 x 16.5 mm, 4 parts (0 on the bottom side), 5 nets.
