ThanicsRobotics/ProjectHaloCAD/ECAD-Files/EAGLE-Files/ThanicsHalo/Drone V2/LED Bar Board/LED Bar Board.brd

## EAGLE design ECAD-Files/EAGLE-Files/ThanicsHalo/Drone V2/LED Bar Board/LED Bar Board.brd (2018-02-16, an earlier design)

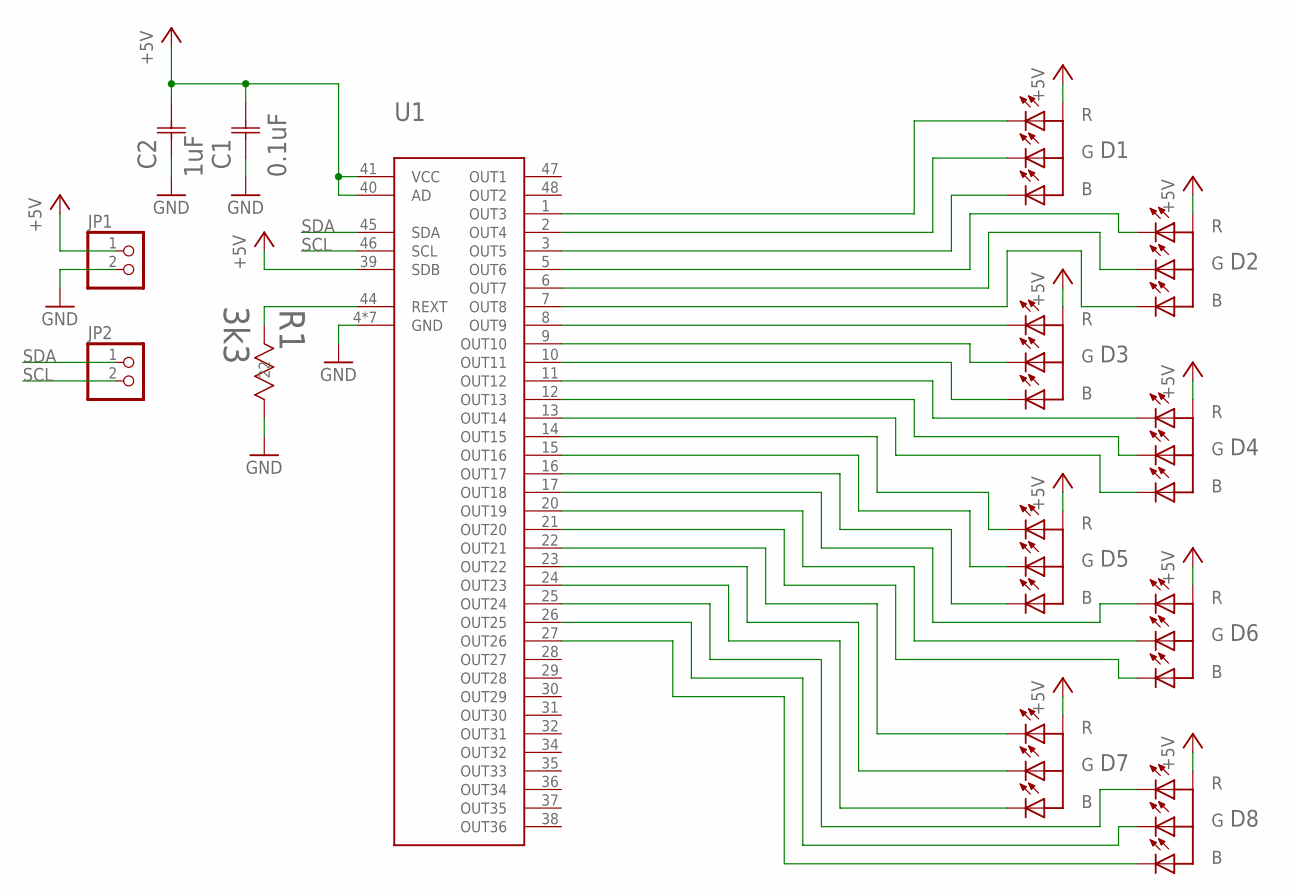
[picture p59: schematic LED Bar Board.sch]

Parts:
C1: 0.1uF; 0805
C2: 1uF; YAG_CC0805
D1, D2, D3, D4, D5, D6, D7, D8: ASMB-MTB0-0A3A2; ASMB-MTB0_LED
JP1, JP2: PINHD-1X2; 1X02
R1: 3k3; RC1206N-M
U1: IS31FL3236; TQFP-48

Connections:
+5V: C1.2, C2.2 (22), D1.1 (A), D2.1 (A), D3.1 (A), D4.1 (A), D5.1 (A), D6.1 (A), D7.1 (A), D8.1 (A), JP1.1, U1.39 (SDB), U1.40 (AD), U1.41 (VCC)
GND: C1.1, C2.1 (11), JP1.2, R1.1 (11), U1.4 (GND), U1.18 (GND), U1.19 (GND), U1.33 (GND), U1.42 (GND), U1.43 (GND), U1.EP (GND)
unnamed: D1.4 (R), U1.1 (OUT3)
unnamed: D1.3 (G), U1.2 (OUT4)
unnamed: D2.3 (G), U1.6 (OUT7)
unnamed: D1.2 (B), U1.3 (OUT5)
unnamed: D2.4 (R), U1.5 (OUT6)
unnamed: R1.2 (22), U1.44 (REXT)
unnamed: D3.4 (R), U1.8 (OUT9)
unnamed: D3.3 (G), U1.9 (OUT10)
unnamed: D3.2 (B), U1.10 (OUT11)
unnamed: D4.4 (R), U1.11 (OUT12)
unnamed: D4.3 (G), U1.12 (OUT13)
unnamed: D4.2 (B), U1.13 (OUT14)
unnamed: D5.4 (R), U1.14 (OUT15)
unnamed: D5.3 (G), U1.15 (OUT16)
unnamed: D5.2 (B), U1.16 (OUT17)
unnamed: D6.4 (R), U1.17 (OUT18)
unnamed: D6.3 (G), U1.20 (OUT19)
unnamed: D6.2 (B), U1.21 (OUT20)
unnamed: D7.4 (R), U1.22 (OUT21)
unnamed: D7.3 (G), U1.23 (OUT22)
unnamed: D7.2 (B), U1.24 (OUT23)
unnamed: D8.4 (R), U1.25 (OUT24)
unnamed: D8.3 (G), U1.26 (OUT25)
unnamed: D8.2 (B), U1.27 (OUT26)
unnamed: D2.2 (B), U1.7 (OUT8)
SCL: JP2.2, U1.46 (SCL)
SDA: JP2.1, U1.45 (SDA)

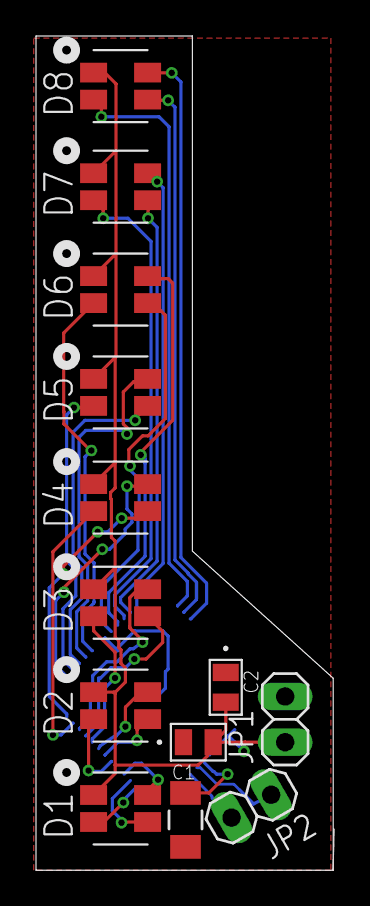
[picture p60: board LED Bar Board.brd from above]

Board: 2 copper layers, 16.5 x 46.3 mm, 14 parts (1 on the bottom side), 29 nets.
