ThanicsRobotics/ProjectHaloCAD/ECAD-Files/EAGLE-Files/ThanicsHalo/Drone V2/Battery Display Board/Battery Display Board.brd

## EAGLE design ECAD-Files/EAGLE-Files/ThanicsHalo/Drone V2/Battery Display Board/Battery Display Board.brd (2018-02-16, an earlier design)

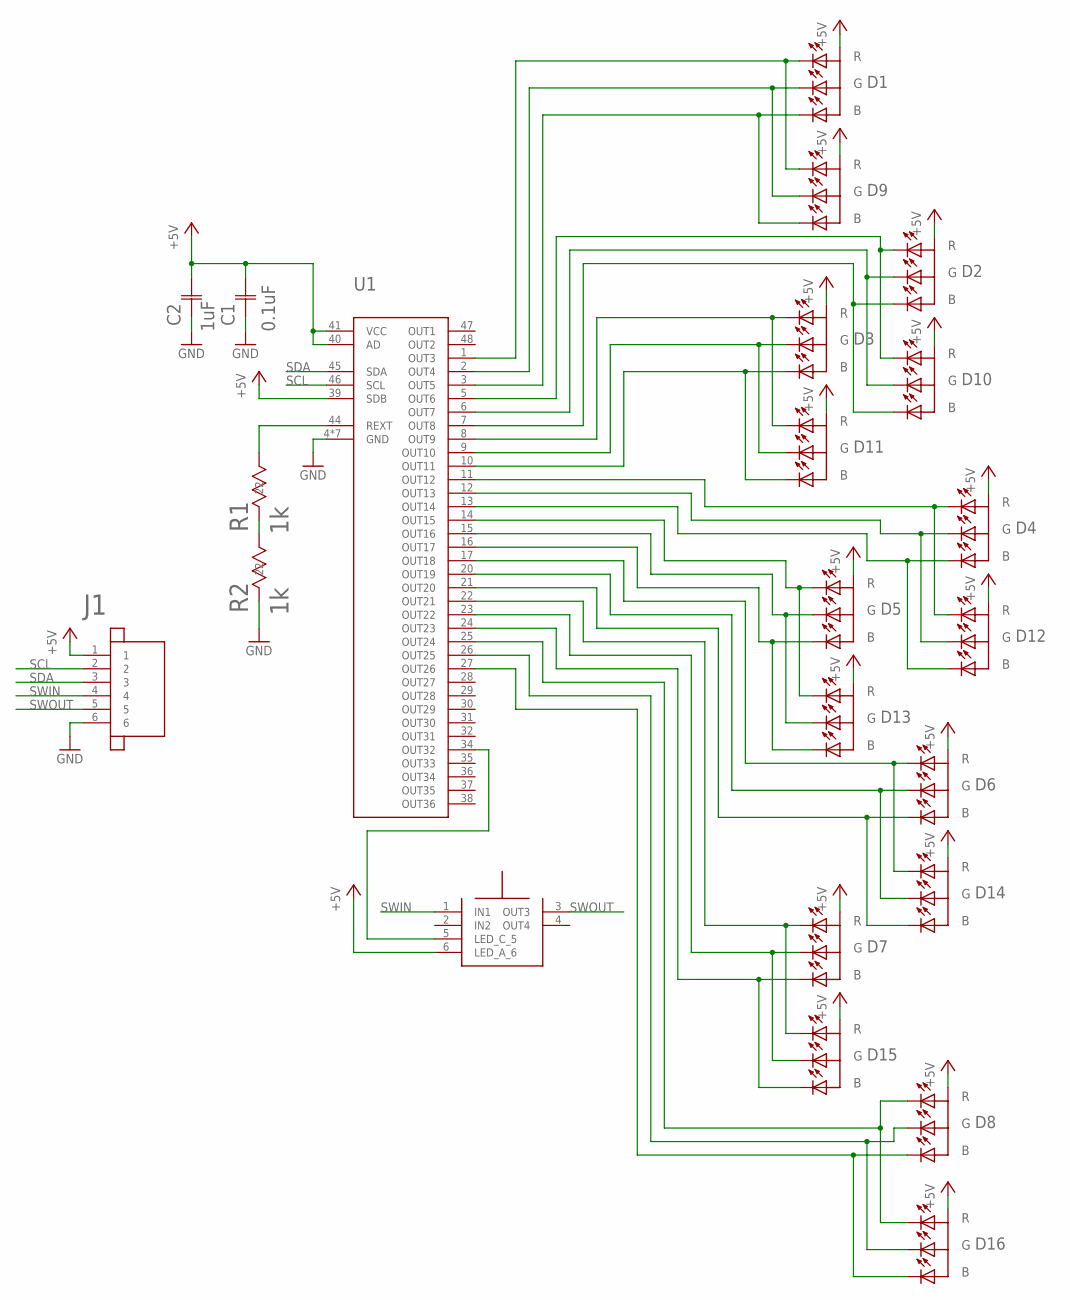
[picture p61: schematic Battery Display Board.sch]

Parts:
C1: 0.1uF; 0805
C2: 1uF; YAG_CC0805
D1, D2, D3, D4, D5, D6, D7, D8, D9, D10, D11, D12, D13, D14, D15, D16: ASMB-MTB0-0A3A2; ASMB-MTB0_LED
J1: JST_SH_6POS_SIDE
R1, R2: 1k; RC0603N-M
U1: IS31FL3236; TQFP-48
U$2: LED_TACT_SWITCH

Connections:
+5V: C1.2, C2.2 (22), D1.1 (A), D2.1 (A), D3.1 (A), D4.1 (A), D5.1 (A), D6.1 (A), D7.1 (A), D8.1 (A), D9.1 (A), D10.1 (A), D11.1 (A), D12.1 (A), D13.1 (A), D14.1 (A), D15.1 (A), D16.1 (A), J1.1, U1.39 (SDB), U1.40 (AD), U1.41 (VCC), U$2.6 (LED_A_6)
GND: C1.1, C2.1 (11), J1.6, R2.2 (22), U1.4 (GND), U1.18 (GND), U1.19 (GND), U1.33 (GND), U1.42 (GND), U1.43 (GND), U1.EP (GND)
unnamed: D1.4 (R), D9.4 (R), U1.1 (OUT3)
unnamed: D1.3 (G), D9.3 (G), U1.2 (OUT4)
unnamed: D2.3 (G), D10.3 (G), U1.6 (OUT7)
unnamed: D1.2 (B), D9.2 (B), U1.3 (OUT5)
unnamed: D2.4 (R), D10.4 (R), U1.5 (OUT6)
unnamed: R1.1 (11), U1.44 (REXT)
unnamed: D3.4 (R), D11.4 (R), U1.8 (OUT9)
unnamed: D3.3 (G), D11.3 (G), U1.9 (OUT10)
unnamed: D3.2 (B), D11.2 (B), U1.10 (OUT11)
unnamed: D4.4 (R), D12.4 (R), U1.11 (OUT12)
unnamed: D4.3 (G), D12.3 (G), U1.12 (OUT13)
unnamed: D4.2 (B), D12.2 (B), U1.13 (OUT14)
unnamed: D5.4 (R), D13.4 (R), U1.14 (OUT15)
unnamed: D5.3 (G), D13.3 (G), U1.15 (OUT16)
unnamed: D5.2 (B), D13.2 (B), U1.16 (OUT17)
unnamed: D6.4 (R), D14.4 (R), U1.17 (OUT18)
unnamed: D6.3 (G), D14.3 (G), U1.20 (OUT19)
unnamed: D6.2 (B), D14.2 (B), U1.21 (OUT20)
unnamed: D7.4 (R), D15.4 (R), U1.22 (OUT21)
unnamed: D7.3 (G), D15.3 (G), U1.23 (OUT22)
unnamed: D7.2 (B), D15.2 (B), U1.24 (OUT23)
unnamed: D8.4 (R), D16.4 (R), U1.25 (OUT24)
unnamed: D8.3 (G), D16.3 (G), U1.26 (OUT25)
unnamed: D8.2 (B), D16.2 (B), U1.27 (OUT26)
unnamed: D2.2 (B), D10.2 (B), U1.7 (OUT8)
unnamed: R1.2 (22), R2.1 (11)
unnamed: U1.34 (OUT32), U$2.5 (LED_C_5)
SCL: J1.2, U1.46 (SCL)
SDA: J1.3, U1.45 (SDA)
SWIN: J1.4, U$2.1 (IN1)
SWOUT: J1.5, U$2.3 (OUT3)

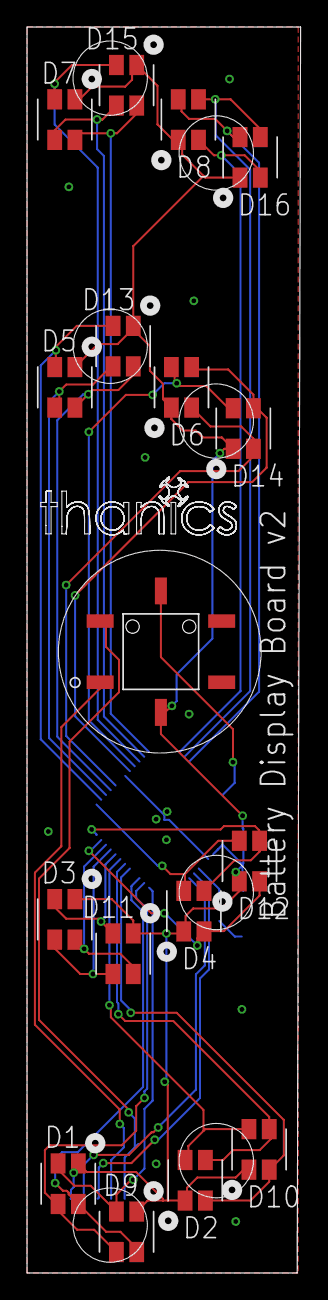
[picture p62: board Battery Display Board.brd from above]

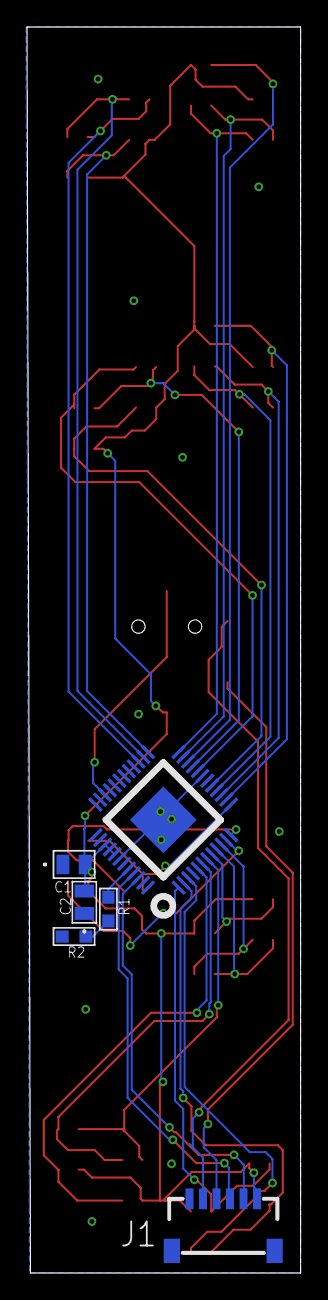
[picture p63: board Battery Display Board.brd from below]

Board: 2 copper layers, 20.2 x 92.2 mm, 23 parts (6 on the bottom side), 33 nets.
