ThanicsRobotics/ProjectHaloCAD/ECAD-Files/EAGLE-Files/ThanicsHalo/Drone V1/Battery Button Board/Battery Button Board.brd

## EAGLE design ECAD-Files/EAGLE-Files/ThanicsHalo/Drone V1/Battery Button Board/Battery Button Board.brd (2018-02-16, an earlier design)

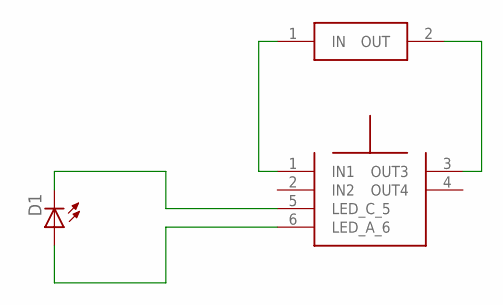
[picture p64: schematic Battery Button Board.sch]

Parts:
D1: LED; XH_CONNECTOR
S1: SWITCH_CONNECTOR; XH_CONNECTOR
U$1: LED_TACT_SWITCH

Connections:
GND: D1.2 (C), U$1.5 (LED_C_5)
unnamed: D1.1 (A), U$1.6 (LED_A_6)
unnamed: S1.1 (IN), U$1.1 (IN1)
unnamed: S1.2 (OUT), U$1.3 (OUT3)

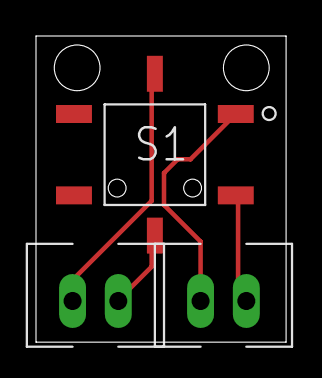
[picture p65: board Battery Button Board.brd from above]

Board: 2 copper layers, 13.9 x 17.0 mm, 3 parts (0 on the bottom side), 4 nets.
