ThanicsRobotics/ProjectHaloCAD/ECAD-Files/EAGLE-Files/ThanicsHalo/Controller/JoystickBulkBoard/JoystickBulkBoard.brd

## EAGLE design ECAD-Files/EAGLE-Files/ThanicsHalo/Controller/JoystickBulkBoard/JoystickBulkBoard.brd (2018-07-26)

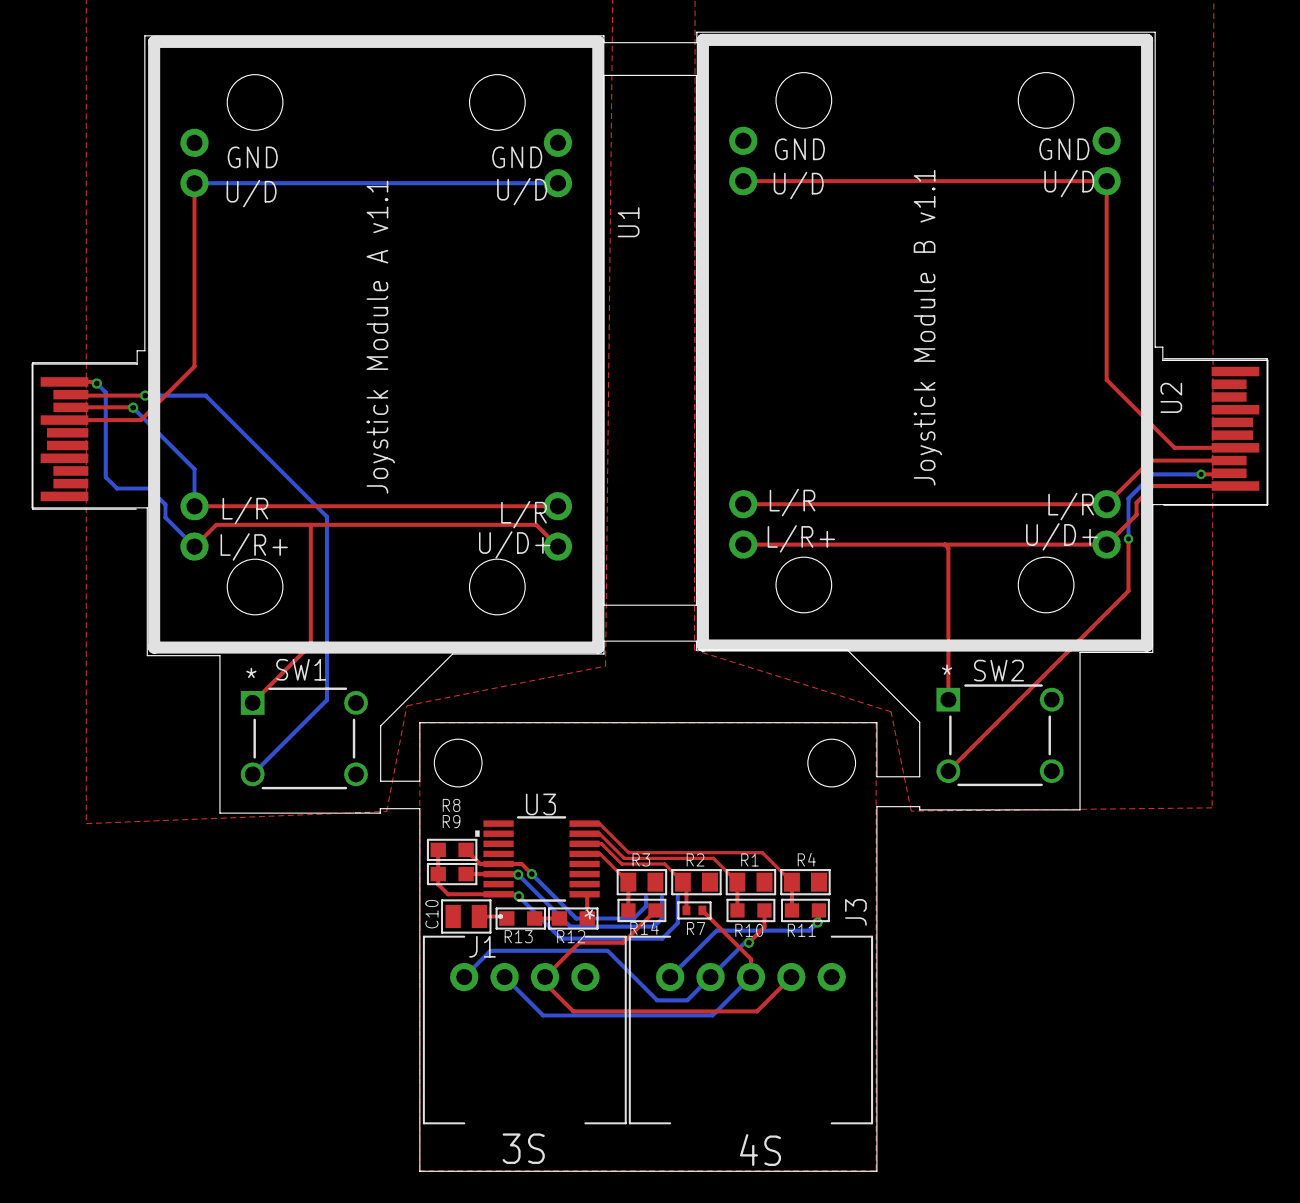
[picture p66: board JoystickBulkBoard.brd from above]

Board: 2 copper layers, 77.7 x 71.7 mm, 23 parts (1 on the bottom side), 25 nets.

Parts:
C10: 0.1uF; 0805
J1: JST-XH_4POS
J2: JST_SH_4POS
J3: JST-XH_5POS
R1, R2, R3, R4: 10k 0.1%; RC0805N
R7: 15.6k; R0402
R8, R9, R12, R13: 1k; RC0603N-M
R10: 28.4k; R0603
R11: 41.2k; R0603
R14: 2.74k; R0603
SW1, SW2: 2-1825910-7; SW4_1825910-G
U1, U2: 27800-JOYSTICK
U3: MAX11608EEE+21-0055H_16-M; 21-0055H_16-M
U$1, U$2: EDGE_CONNECTOR_20POS_CONTACTS

Connections:
+3V1: SW2.1, U2.1, U2.3, U$1.11
+3V2: J2.1, R8.1, R9.1, U3.16
+3V3: SW1.1, U1.1, U1.3, U$2.11
C1: R3.2, R14.1, U3.5
C2: R2.2, R7.1, U3.6
C3: R1.2, R10.1, U3.7
C4: R4.2, R11.1, U3.8
GND: U1.6, U1.8, U$2.15
GND1: U2.6, U2.8, U$1.15
GND2: C10.2, J1.4, J2.4, J3.5, R1.1, R2.1, R3.1, R4.1, U3.15
I2C_SCL: J2.3, R8.2, U3.13
I2C_SDA: J2.2, R9.2, U3.14
J2_SW: SW1.3, U$2.12
J2_SW1: SW2.3, U$1.12
unnamed: R12.1, U3.1
unnamed: J1.3, J3.4, R14.2
unnamed: J1.2, J3.3, R7.2
unnamed: J1.1, J3.2, R10.2
unnamed: J3.1, R11.2
unnamed: R12.2, R13.1
unnamed: C10.1, R13.2
VRX: U1.2, U1.4, U$2.13
VRX1: U2.2, U2.4, U$1.13
VRY: U1.5, U1.7, U$2.14
VRY1: U2.5, U2.7, U$1.14
