ThanicsRobotics/ProjectHaloCAD/ECAD-Files/EAGLE-Files/ThanicsHalo/Drone V3/Bulk Board/BulkBoard2.brd

## EAGLE design ECAD-Files/EAGLE-Files/ThanicsHalo/Drone V3/Bulk Board/BulkBoard2.brd (2018-07-10)

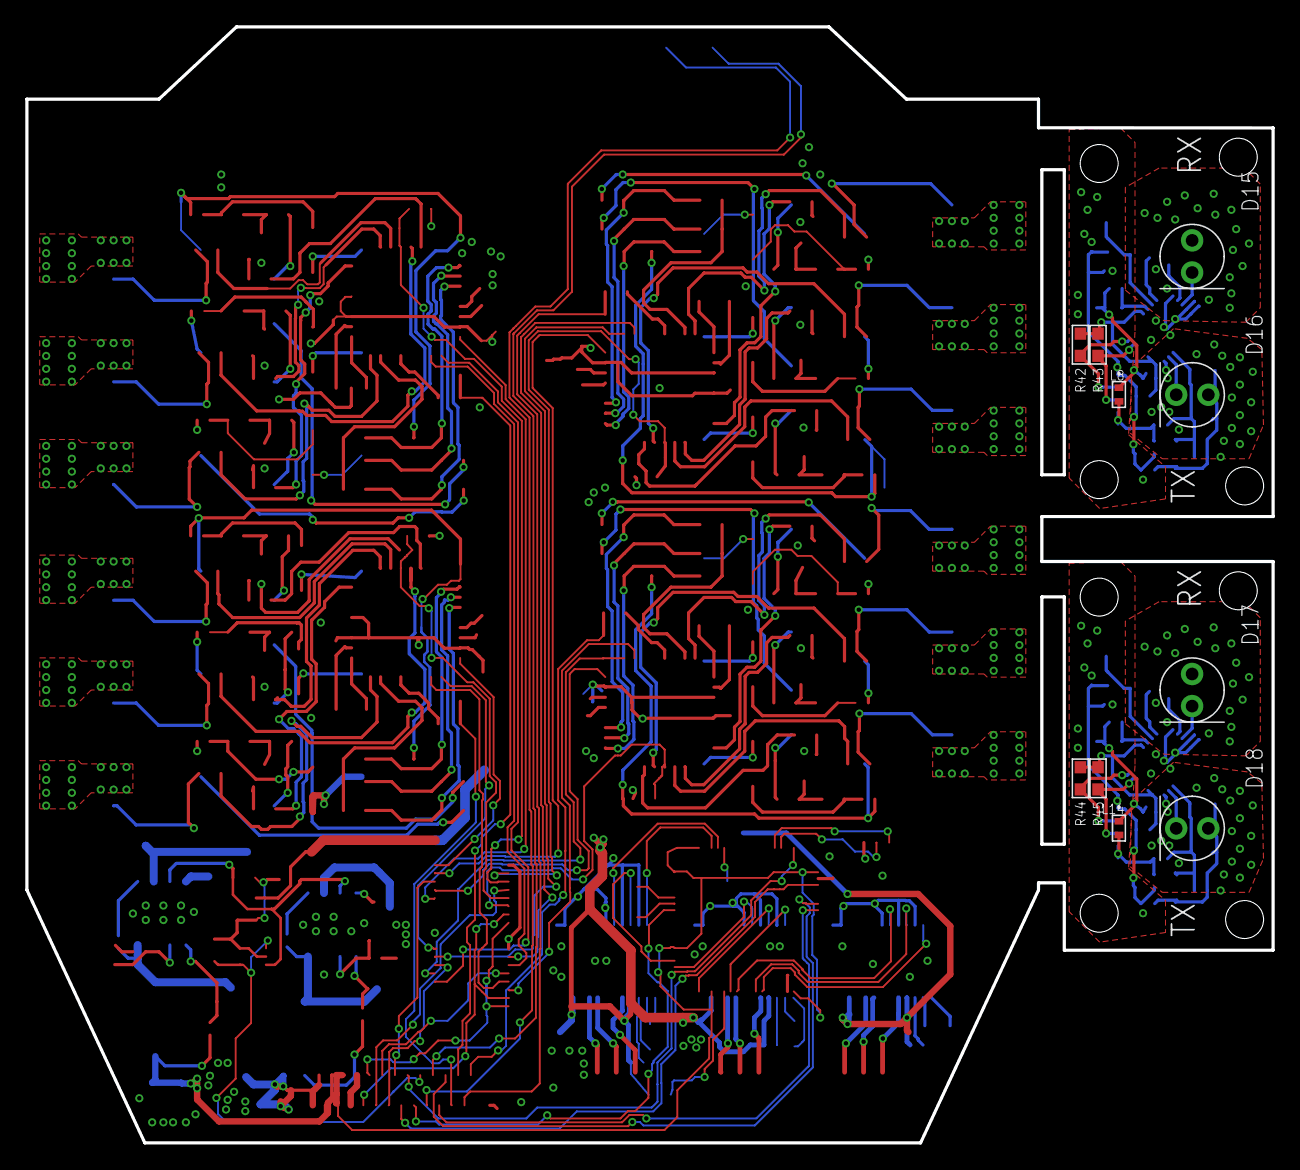
[picture p67: board BulkBoard2.brd from above]

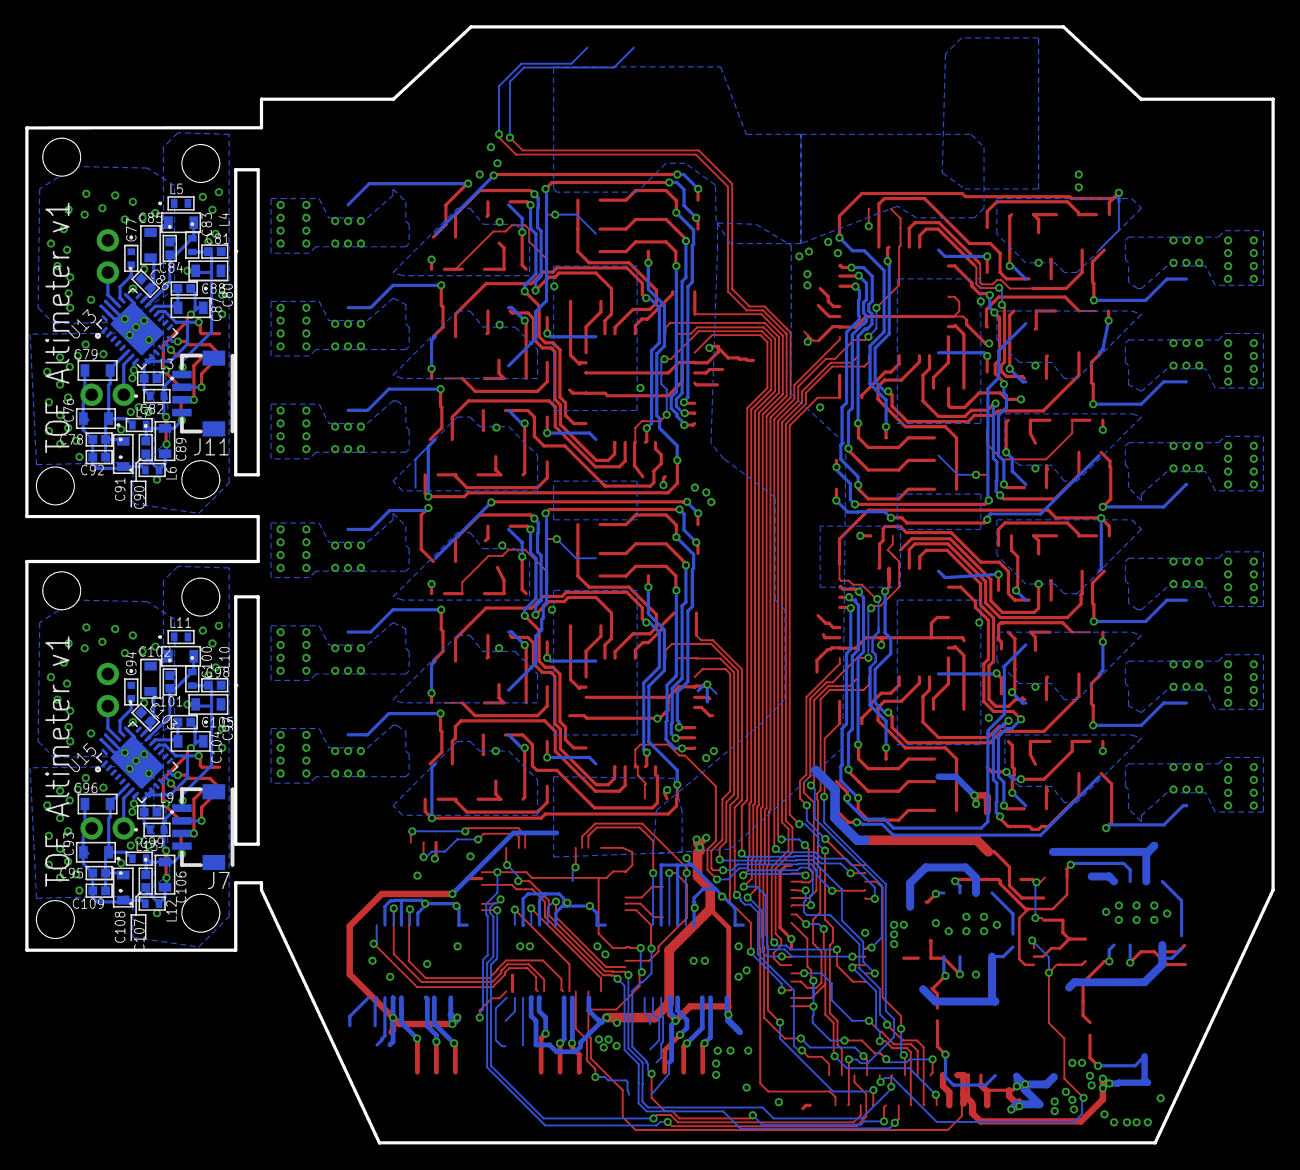
[picture p68: board BulkBoard2.brd from below]

Board: 4 copper layers, 98.6 x 88.3 mm, 58 parts (48 on the bottom side), 30 nets.

Parts:
C76, C79, C80, C83, C85, C87, C89, C91, C93, C96, C97, C100, C102, C104, C106, C108: 1uF; 0603_CAPACITOR
C77, C94: 6pF; 0402_CAPACITOR
C78, C81, C82, C84, C86, C88, C90, C92, C95, C98, C99, C101, C103, C105, C107, C109: 0.1uF; 0402-M
D15, D17: SFH203FA; 5MM_LED
D16, D18: SFH4550; 5MM_LED
J7, J11: JST_SH_4POS
L3, L4, L5, L6, L7, L8, L9, L10, L11, L12, L13, L14: MMZ1005S182ET000IND_1005-M; IND_1005-M
R42, R43, R44, R45: 1k; RC0603N-M
U13, U15: OPT3101; 28-VQFN

Connections:
+3V1: C80.1, C81.2, C89.1, C90.2, J11.1, L3.2, L4.2, L6.2
+3V2: C87.1, C88.2, U13.19
+3V4: C97.1, C98.2, C106.1, C107.2, J7.1, L9.2, L10.2, L12.2
+3V5: C104.1, C105.2, U15.19
AGND: C77.1, C83.2, C84.1, C85.2, C86.1, D15.A, L5.1, U13.23, U13.26, U13.27, U13.29
AGND1: C94.1, C100.2, C101.1, C102.2, C103.1, D17.A, L11.1, U15.23, U15.26, U15.27, U15.29
AVCC: C83.1, C84.2, L4.1, U13.20
AVCC1: C100.1, C101.2, L10.1, U15.20
GND1: C80.2, C81.1, C89.2, C90.1, J11.4, J11.P$5, J11.P$6, L5.2, L7.2, L8.2
GND2: C97.2, C98.1, C106.2, C107.1, J7.4, J7.P$5, J7.P$6, L11.2, L13.2, L14.2
GNDIO: C82.1, C87.2, C88.1, L8.1, U13.3, U13.4, U13.5, U13.8
GNDIO1: C99.1, C104.2, C105.1, L14.1, U15.3, U15.4, U15.5, U15.8
I2C_SCL: J11.3, R43.2, U13.13
I2C_SCL1: J7.3, R45.2, U15.13
I2C_SDA: J11.2, R42.2, U13.14
I2C_SDA1: J7.2, R44.2, U15.14
unnamed: D16.C, U13.7
unnamed: C77.2, U13.24
unnamed: D15.C, U13.25
unnamed: C85.1, C86.2, U13.21
unnamed: D18.C, U15.7
unnamed: C94.2, U15.24
unnamed: D17.C, U15.25
unnamed: C102.1, C103.2, U15.21
VCCIO: C82.2, L3.1, R42.1, R43.1, U13.9, U13.10, U13.18
VCCIO1: C99.2, L9.1, R44.1, R45.1, U15.9, U15.10, U15.18
VDDLED: C76.2, C78.2, C79.2, C91.1, C92.2, D16.A, L6.1
VDDLED1: C93.2, C95.2, C96.2, C108.1, C109.2, D18.A, L12.1
VSS: C76.1, C78.1, C79.1, C91.2, C92.1, L7.1, U13.6
VSS1: C93.1, C95.1, C96.1, C108.2, C109.1, L13.1, U15.6
