ThanicsRobotics/ProjectHaloCAD/ECAD-Files/EAGLE-Files/ThanicsHalo/Drone V2/Bulk Board 3/Joystick Module A.brd

## EAGLE design ECAD-Files/EAGLE-Files/ThanicsHalo/Drone V2/Bulk Board 3/Joystick Module A.brd (2018-02-16, an earlier design)

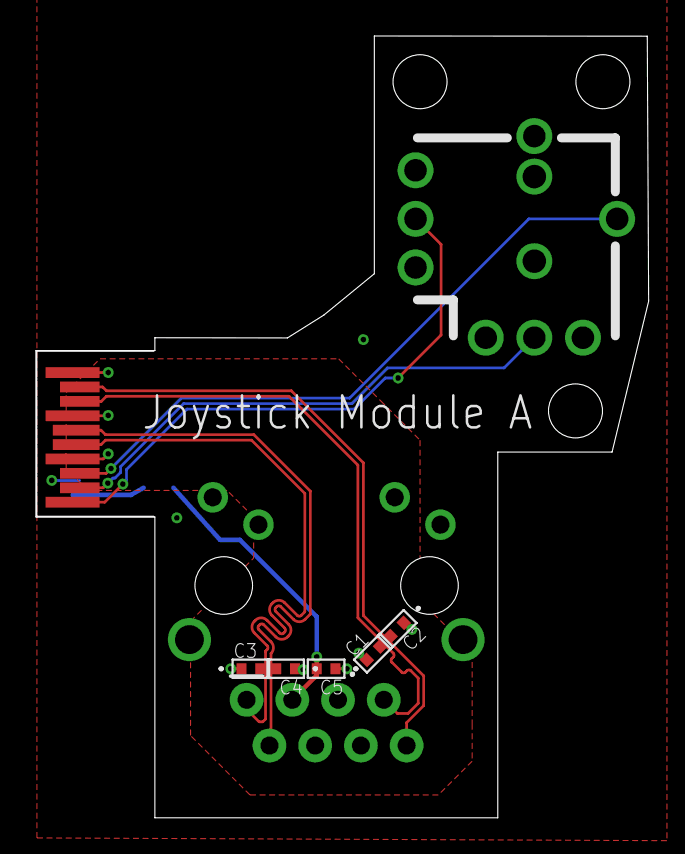
[picture p69: board ECAD-Files/EAGLE-Files/ThanicsHalo/Drone V2/Bulk Board 3/Joystick Mod… from above]

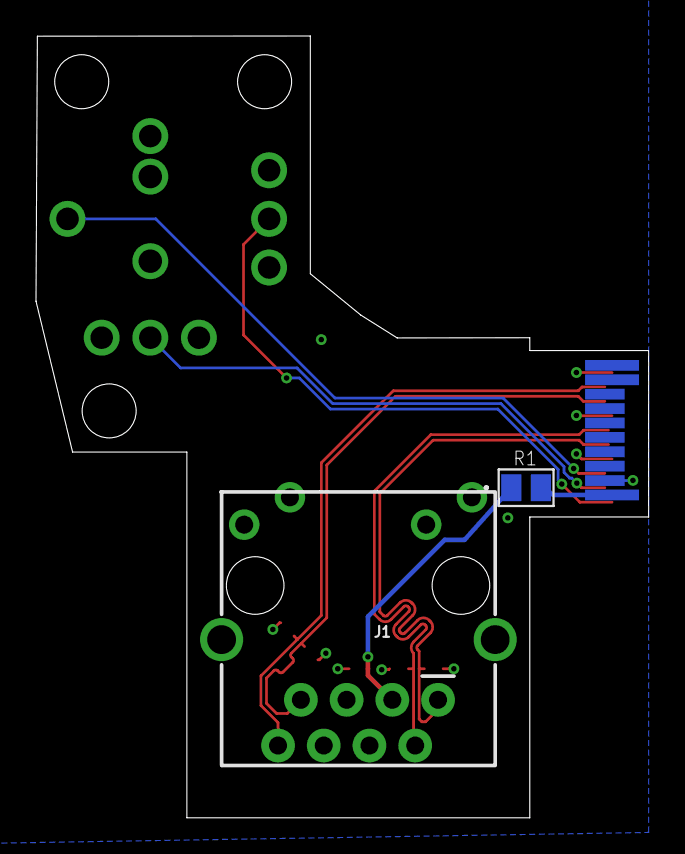
[picture p70: board ECAD-Files/EAGLE-Files/ThanicsHalo/Drone V2/Bulk Board 3/Joystick Mod… from below]

Board: 4 copper layers, 34.0 x 43.4 mm, 9 parts (2 on the bottom side), 11 nets.

Parts:
C1, C2, C3, C4: 16pF; G-155-M
C5: 22nF; G-155-M
J1: MAGJACK
R1: 10R; STA_RNCP0805-M
U$1: JOYSTICK"; JOYSTICK
U$2: EDGE_CONNECTOR_20POS_CONTACTS

Connections:
3.3V_A: R1.2, U$2.1
+3V3: U$1.1, U$1.1', U$1.A, U$2.2
GND: C1.1, C2.1, C3.1, C4.1, C5.1, J1.10, J1.12, J1.M1, J1.M2, U$1.3, U$1.3', U$2.11, U$2.14, U$2.17
J2_SW: U$1.B, U$2.18
unnamed: C5.2, J1.3, R1.1
RX_N: C4.2, J1.2, U$2.15
RX_P: C3.2, J1.1, U$2.16
TX_N: C2.2, J1.8, U$2.12
TX_P: C1.2, J1.7, U$2.13
VRX: U$1.2, U$2.20
VRY: U$1.2', U$2.19
