ThanicsRobotics/ProjectHaloCAD/ECAD-Files/EAGLE-Files/ThanicsHalo/Drone V2/Bulk Board 3/BulkBoard3.brd

## EAGLE design ECAD-Files/EAGLE-Files/ThanicsHalo/Drone V2/Bulk Board 3/BulkBoard3.brd (2018-02-16, an earlier design)

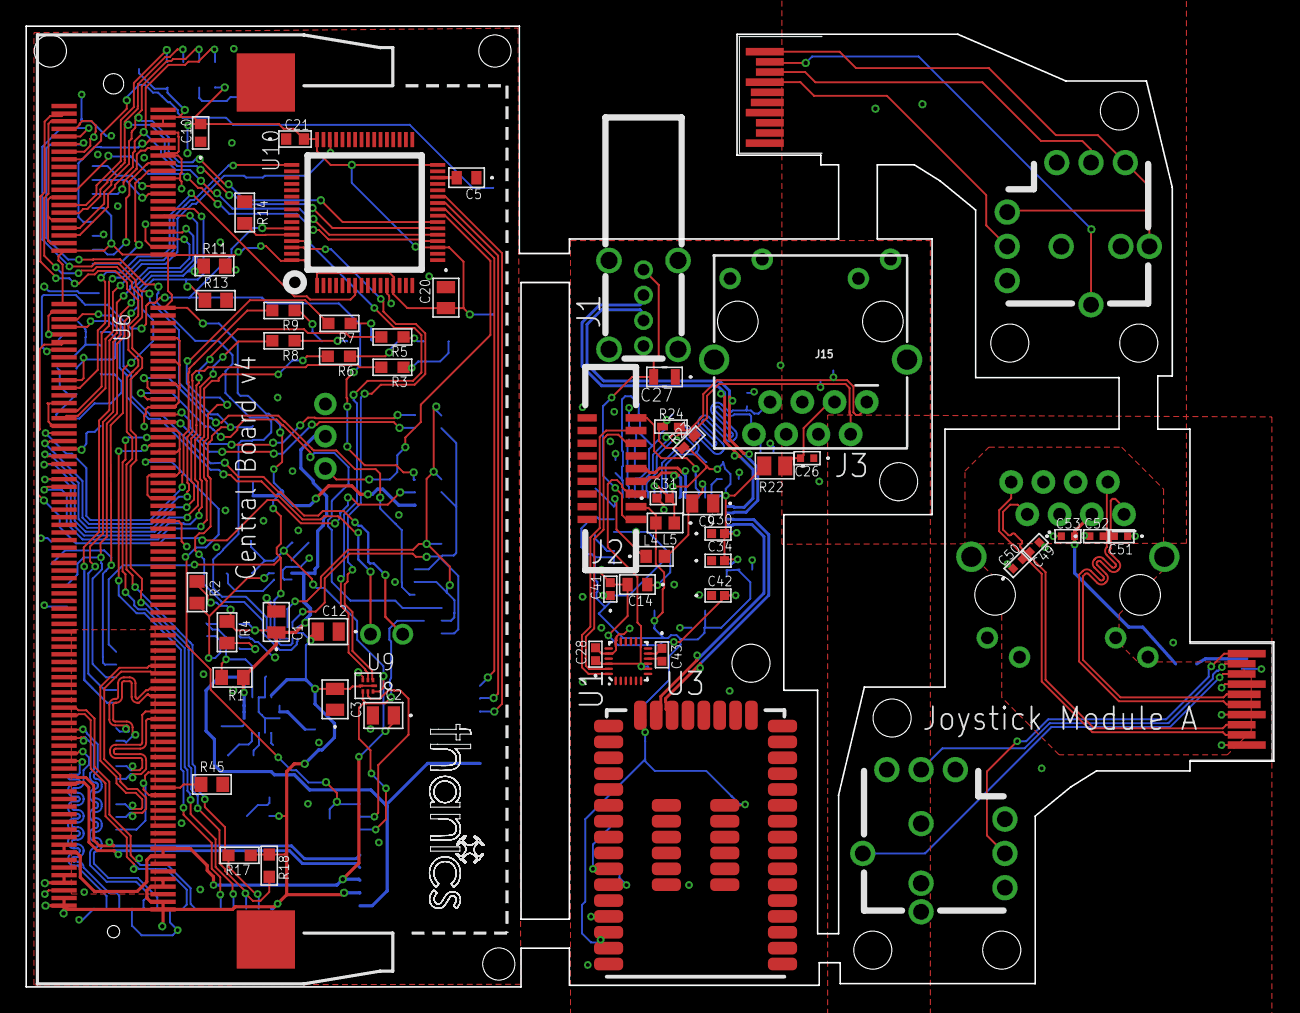
[picture p71: board BulkBoard3.brd from above]

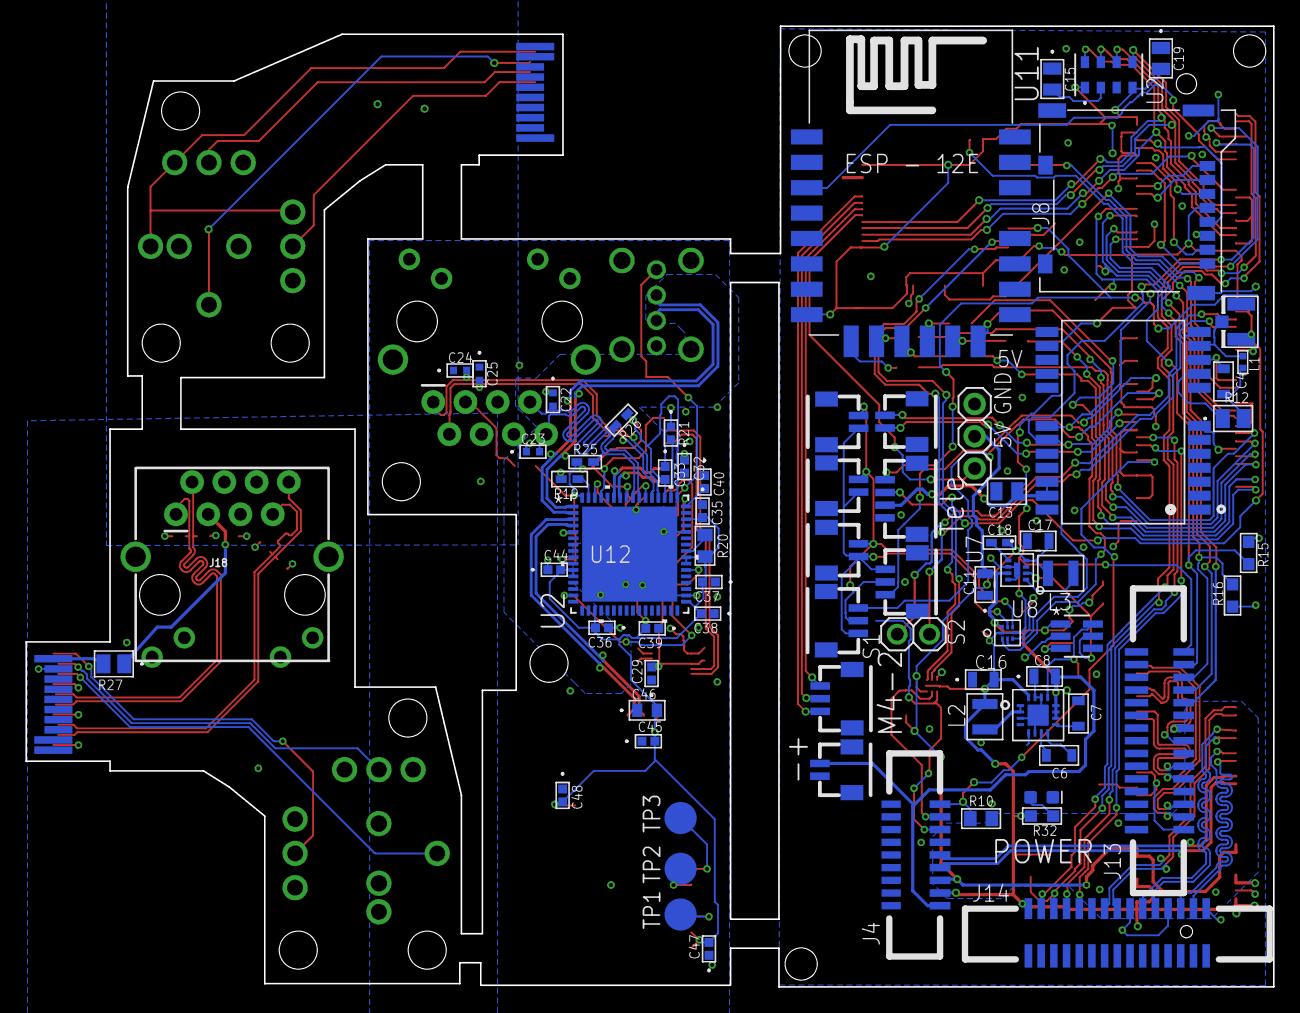
[picture p72: board BulkBoard3.brd from below]

Board: 4 copper layers, 98.3 x 75.7 mm, 128 parts (72 on the bottom side), 136 nets.

Parts:
C1, C2, C3, C12, C13, C20: 0.1uF; 0805
C4, C6, C7: 10nF; 0603_CAPACITOR
C5, C14, C46: 4.7uF; 0603-M
C8, C11, C17: 10uF; G-21
C9, C15, C19: 1uF; YAG_CC0805
C10, C21: 2.2uF; G-188-M
C16, C27: 22uF; G-21
C18: 560pF; CC0402N-M
C22, C23, C24, C25, C49, C50, C51, C52: 16pF; G-155-M
C26, C53: 22nF; G-155-M
C28, C29, C30, C31, C32, C33, C34, C35, C36, C37, C38, C39, C40, C41, C42, C43, C44, C45, C47, C48: 0.1uF; 0402-M
D1: GREEN; LED-0603
J1, J2, J6, J7, J9: JST_SH_2POS
J3: JST_SH_4POS
J4, J17: 9POS_FFC_CONNECTOR
J5: U.FL
J8: MICROSD
J10, J11, J12: JST_SH_3POS
J13, J14: 15POS_FFC_CONNECTOR
J15, J18: MAGJACK
J16: USB_A_VERTICAL
JP1: 1X02
JP2: 1X03
L1: 27 nH; 0402_INDUCTOR
L2, L3: 470nH; 1008_INDUCTOR
L4, L5: FB; IND_BLM18_0603-M
R1, R2, R4, R10, R11, R13, R14, R20, R45: 10k; RC0805N
R3, R5, R6, R7, R8, R9, R32: 20R; RC0603N-M
R12: 10; STA_RNCP0805-M
R15, R16, R17, R18: 1k; RC0603N-M
R19: 12k; RC0402N-M
R21: 12.4k; YAG_R0402-M
R22, R27: 10R; STA_RNCP0805-M
R23, R24, R25, R26: 49R9; RC0402N-M
TP1, TP2, TP3: TPB2,54; B2,54
U1: QFN40P300X300X105-25N
U2: LGA8-M
U3: LM3880MF-1AA/NOPBMF06A-M; MF06A-M
U4: NEO-M8
U5: TPS6209; VQFN16
U6: SO-DIMM
U7: MIC23050; MLF(ML)_8PIN
U8, U9: 8-UMLP
U10: LQFP64
U11: ESP12E-SMD
U12: QFN64_9X9MC-M
U13: WGM110A
U$1, U$3: JOYSTICK"; JOYSTICK
U$2, U$4: EDGE_CONNECTOR_20POS_CONTACTS

Connections:
1.8V: C2.1, C17.2, C18.2, J4.3, L3.P$2, U6.183, U6.184, U6.185, U6.186, U7.4, U9.8
1.8V1: C28.1, C29.2, J17.3, U1.8, U1.9, U1.13, U1.22
3.3V_A: C30.2, C31.2, C32.2, C33.2, C34.2, L5.1, R22.2, R23.1, R24.1, R25.1, R26.1, U12.5, U12.10, U12.49, U12.51, U12.54, U12.57, U12.64
3.3V_A1: R27.2, U$2.1
+3V1: C35.2, C36.2, C37.2, C38.2, C39.2, C44.2, C45.2, C46.2, C47.2, C48.2, J17.2, L5.2, R20.2, U12.11, U12.12, U12.19, U12.27, U12.33, U12.39, U12.40, U12.46, U13.24, U13.38, U13.39, U13.51
+3V2: U$1.1, U$1.1', U$1.A, U$2.2
+3V3: C3.2, C10.2, C12.2, C13.2, C16.2, C19.2, C20.2, C21.2, J3.3, J4.2, J8.4, J13.15, J14.15, L2.P$2, R15.1, R16.1, R17.1, R18.1, R32.2, U2.1, U2.4, U4.22, U4.23, U5.16, U6.4, U6.6, U6.39, U6.40, U6.41, U6.42, U6.191, U6.192, U6.193, U6.194, U6.197, U6.198, U6.199, U6.200, U8.1, U8.5, U9.1, U9.5, U10.1, U10.13, U10.19, U10.32, U10.48, U10.64, U11.VCC
+3V4: U$3.1, U$3.1', U$3.A, U$4.11
+5V: C1.1, C8.2, C11.2, J4.1, J6.1, JP2.2, R1.1, R2.1, R4.1, U3.1, U5.10, U5.11, U5.12, U7.7, U8.8
+5V1: C27.2, J16.1, J17.1
C0_C_N: J13.8, U6.144
C0_C_P: J13.9, U6.142
C0_D0_N: J13.2, U6.138
C0_D0_P: J13.3, U6.136
C0_D1_N: J13.5, U6.150
C0_D1_P: J13.6, U6.148
C0_IO0: J13.11, U6.36
C0_IO1: J13.12, U6.34
C1_C_N: J14.8, U6.149
C1_C_P: J14.9, U6.147
C1_D0_N: J14.2, U6.161
C1_D0_P: J14.3, U6.159
C1_D1_N: J14.5, U6.155
C1_D1_P: J14.6, U6.153
C1_IO0: J14.11, U6.78
C1_IO1: J14.12, U6.76
GND: C1.2, C2.2, C3.1, C4.1, C5.1, C7.1, C8.1, C10.1, C11.1, C12.1, C13.1, C15.1, C16.1, C17.1, C19.1, C20.1, C21.1, D1.C, J3.4, J4.6, J5.P$1, J5.P$2, J6.2, J8.6, J8.9, J8.10, J8.11, J8.12, J8.13, J13.1, J13.4, J13.7, J13.10, J14.1, J14.4, J14.7, J14.10, JP2.3, R10.2, R11.2, R13.2, R14.1, R45.2, U2.3, U3.2, U4.7, U4.10, U4.12, U4.13, U4.24, U5.3, U5.5, U5.6, U5.14, U5.15, U5.17, U6.1, U6.7, U6.8, U6.13, U6.14, U6.19, U6.20, U6.25, U6.26, U6.31, U6.32, U6.37, U6.38, U6.43, U6.44, U6.49, U6.50, U6.55, U6.56, U6.61, U6.62, U6.67, U6.68, U6.73, U6.74, U6.79, U6.80, U6.85, U6.86, U6.91, U6.92, U6.97, U6.98, U6.103, U6.104, U6.109, U6.110, U6.115, U6.116, U6.121, U6.122, U6.127, U6.133, U6.134, U6.139, U6.140, U6.145, U6.146, U6.151, U6.152, U6.157, U6.163, U6.164, U6.169, U6.170, U6.181, U6.182, U6.187, U6.188, U6.195, U6.196, U6.G1, U6.G2, U7.6, U7.8, U7.EP, U8.4, U9.4, U10.12, U10.18, U10.31, U10.47, U10.63, U11.GND
GND1: C9.1, C14.1, C22.1, C23.1, C24.1, C25.1, C26.1, C27.1, C28.2, C29.1, C30.1, C31.1, C32.1, C33.1, C34.1, C35.1, C36.1, C37.1, C38.1, C39.1, C40.1, C41.1, C42.1, C43.1, C44.1, C45.1, C46.1, C47.1, C48.1, J15.10, J15.12, J15.M1, J15.M2, J16.4, J16.P$5, J16.P$6, J16.P$7, J16.P$8, J17.6, R19.2, R21.1, U1.11, U1.18, U1.20, U12.34, U12.44, U12.65, U13.1, U13.16, U13.25, U13.40, U13.42, U13.44, U13.46, U13.48
GND2: C49.1, C50.1, C51.1, C52.1, C53.1, J18.10, J18.12, J18.M1, J18.M2, U$1.3, U$1.3', U$2.11, U$2.14, U$2.17
GND3: U$3.3, U$3.3', U$4.15
GPCLK: J17.9, U12.61
GPCLK1: J4.9, R10.1, U6.82
I2C_MPU_SCL: U9.3, U10.61
I2C_MPU_SDA: U9.2, U10.62
I2C_SCL: U4.19, U6.11, U8.3
I2C_SCL_1V8: J4.7, U9.6
I2C_SCL_5V: J1.2, J2.2, J7.2, J10.2, J11.2, U8.6
I2C_SDA: U4.18, U6.9, U8.2
I2C_SDA_1V8: J4.8, U9.7
I2C_SDA_5V: J1.1, J2.1, J7.1, J10.1, J11.1, U8.7
ID_SD: U6.15, U11.CH_PD
INT_A: J10.3, U6.64
INT_B: J11.3, U6.66
J2_SW: U$1.B, U$2.18
J2_SW1: U$3.B, U$4.12
MOTOR1: JP2.1, U10.24
MOTOR2: J12.1, U10.25
MOTOR3: J12.2, U10.26
MOTOR4: J12.3, U10.27
unnamed: J5.P$3, L1.P$1, U4.11
unnamed: C6.2, U5.7
unnamed: C6.1, U5.8
unnamed: D1.A, R32.1
unnamed: R1.2, U3.6, U5.13
unnamed: R2.2, U3.5, U7.2
unnamed: R3.1, U11.CS0
unnamed: R5.1, U11.MISO
unnamed: R6.1, U11.GPIO9
unnamed: R7.1, U11.GPIO10
unnamed: C5.2, U10.30
unnamed: C15.2, U2.2
unnamed: R12.1, U4.9
unnamed: R8.1, U11.MOSI
unnamed: R9.1, U11.SCLK
unnamed: R14.2, U10.60
unnamed: C43.2, U1.10
unnamed: R20.1, U12.41
unnamed: R19.1, U12.63
unnamed: TP1.TP, U13.37
unnamed: TP2.TP, U13.35
unnamed: TP3.TP, U13.34
unnamed: C4.2, L1.P$2, R12.2
unnamed: C40.2, L4.1, U12.48
unnamed: C7.2, U5.9
unnamed: L2.P$1, U5.1, U5.2
unnamed: C9.2, L4.2, U12.62
unnamed: L3.P$1, U7.1
unnamed: R21.2, U12.50
unnamed: C14.2, C41.2, C42.2, U12.15, U12.38
unnamed: C26.2, J15.3, R22.1
unnamed: C53.2, J18.3, R27.1
unnamed: C18.1, U7.5
unnamed: R45.1, U6.168
NRST: U6.63, U10.7
POWER_SEQ_EN: R4.2, U3.3
RX_N: C25.2, J15.2, R23.2, U12.53
RX_N1: C52.2, J18.2, U$2.15
RX_P: C24.2, J15.1, R24.2, U12.52
RX_P1: C51.2, J18.1, U$2.16
SCL: J17.7, U1.23
SCL0: J13.13, R11.1, R16.2, U6.30
SCL1: J14.13, R18.2, U6.5
SDA: J17.8, U1.24
SDA0: J13.14, R13.1, R15.2, U6.28
SDA1: J14.14, R17.2, U6.3
SDX_CLK: J8.5, U6.10
SDX_CMD: J8.3, U6.12
SDX_D0: J8.7, U6.16
SDX_D1: J8.8, U6.18
SDX_D2: J8.1, U6.22
SDX_D3: J8.2, U6.24
SD_CLK: R9.2, U6.75
SD_CMD: R3.2, U6.77
SD_D0: R5.2, U6.81
SD_D1: R8.2, U6.83
SD_D2: R6.2, U6.87
SD_D3: R7.2, U6.89
SERVO1: JP1.1, U6.45
SERVO2: JP1.2, U6.47
SPI_CS0: U2.5, U6.27
SPI_CS1: U6.23, U10.20
SPI_MISO: U2.6, U6.29, U10.22
SPI_MOSI: U2.7, U6.33, U10.23
SPI_SCLK: U2.8, U6.35, U10.21
SWCLK: U6.69, U10.49
SWDIO: U6.71, U10.46
TX_N: C23.2, J15.8, R25.2, U12.56
TX_N1: C50.2, J18.8, U$2.12
TX_P: C22.2, J15.7, R26.2, U12.55
TX_P1: C49.2, J18.7, U$2.13
UART2_RX: J9.2, U6.72
UART2_TX: J9.1, U6.70
USART1_RX: J3.1, U6.53, U10.59
USART1_TX: J3.2, U6.51
USB_D2_N: J16.2, U12.1
USB_D2_P: J16.3, U12.2
USB_D3_N: U12.3, U13.22
USB_D3_P: U12.4, U13.23
USB_D_N: J4.4, U6.167
USB_D_N1: J17.4, U12.58
USB_D_P: J4.5, U6.165
USB_D_P1: J17.5, U12.59
VRX: U$1.2, U$2.20
VRX1: U$3.2, U$4.13
VRY: U$1.2', U$2.19
VRY1: U$3.2', U$4.14
